SFXShannon/c172-home-sim/parts/mixture/stl/housing.stl

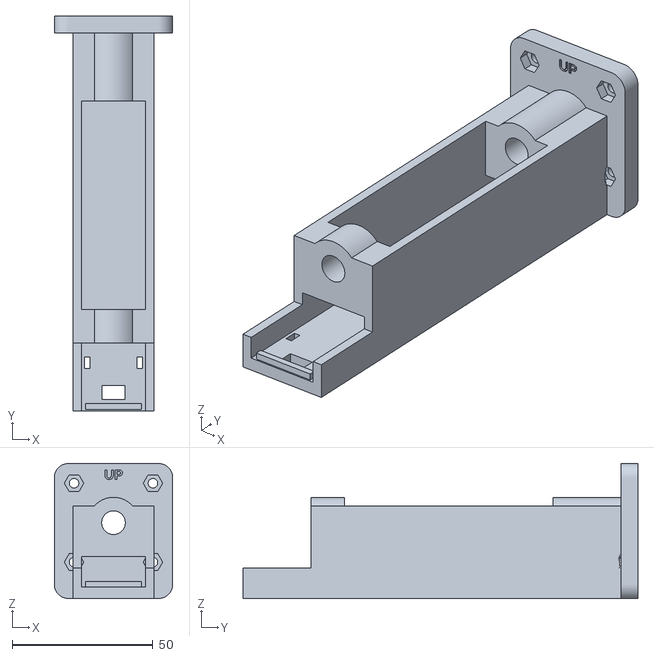
[picture p63: CAD file, 2026-10-08]
parts/mixture/stl/housing.stl
42.0 x 140.0 x 47.9
