SFXShannon/c172-home-sim/parts/panel-extras/stl/stem_clip.stl

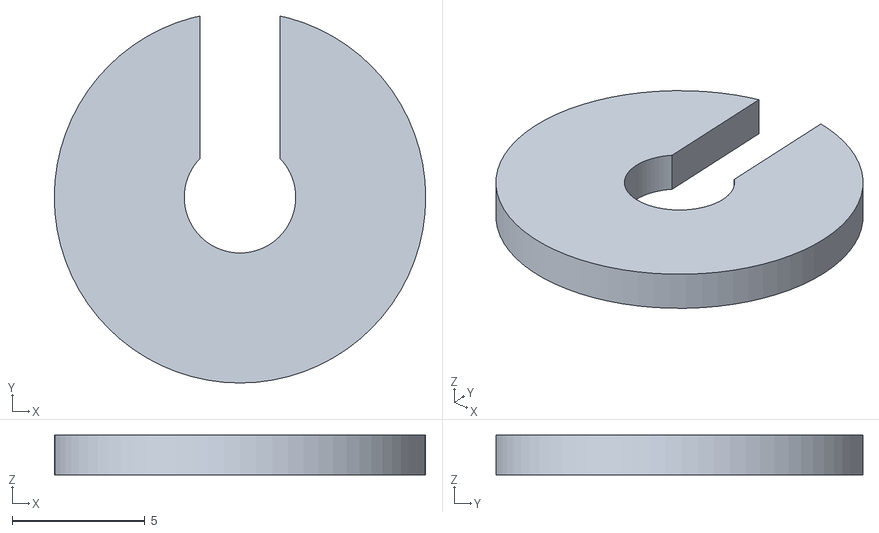
[picture p64: CAD file, 2026-10-08]
parts/panel-extras/stl/stem_clip.stl
14.0 x 13.8 x 1.50
