SFXShannon/c172-home-sim/parts/parking-brake/panel-template/parking_brake_cutout.dxf

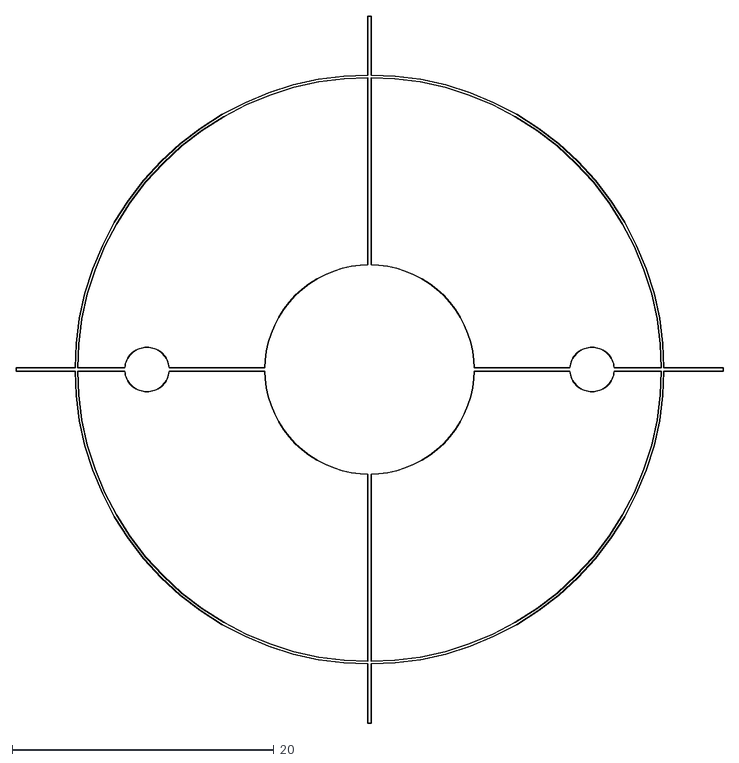
[picture p65: CAD file, 2026-10-08]
parts/parking-brake/panel-template/parking_brake_cutout.dxf
54.0 x 54.0
