SFXShannon/c172-home-sim/parts/parking-brake/stl/housing.stl

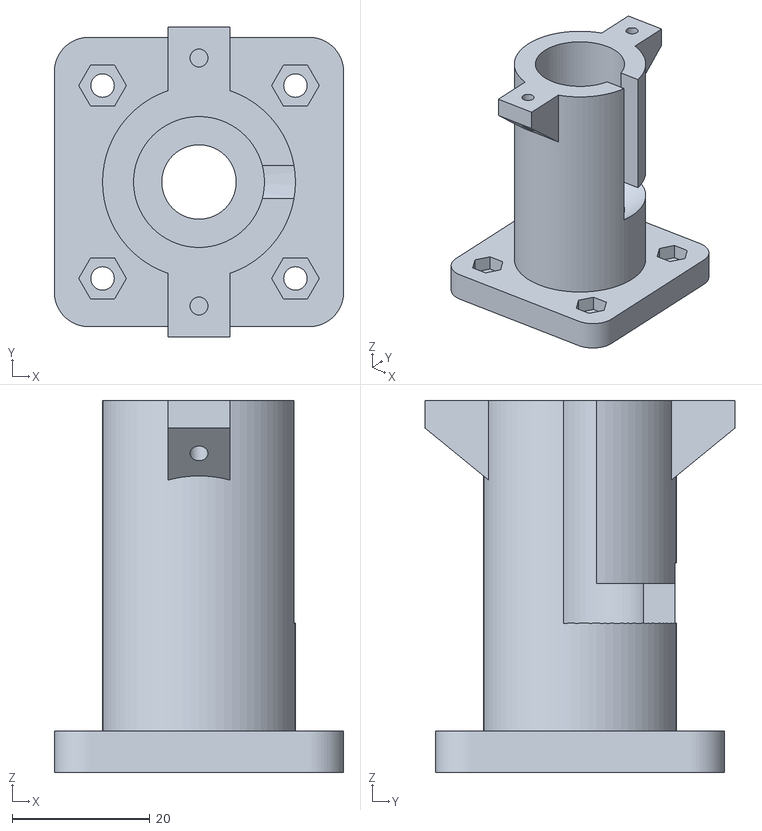
[picture p66: CAD file, 2026-10-08]
parts/parking-brake/stl/housing.stl
42.0 x 45.0 x 54.0
