SFXShannon/c172-home-sim/parts/prop/stl/knob.stl

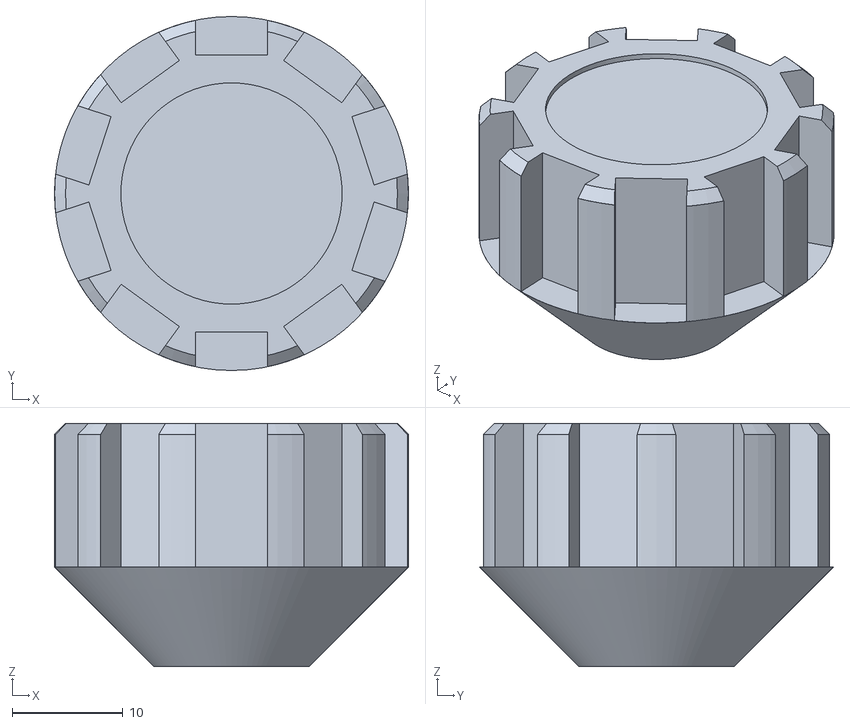
[picture p67: CAD file, 2026-10-08]
parts/prop/stl/knob.stl
32.0 x 32.0 x 22.0
