SFXShannon/c172-home-sim/parts/standby-gauges/panel-template/standby_gauges_cutout.dxf

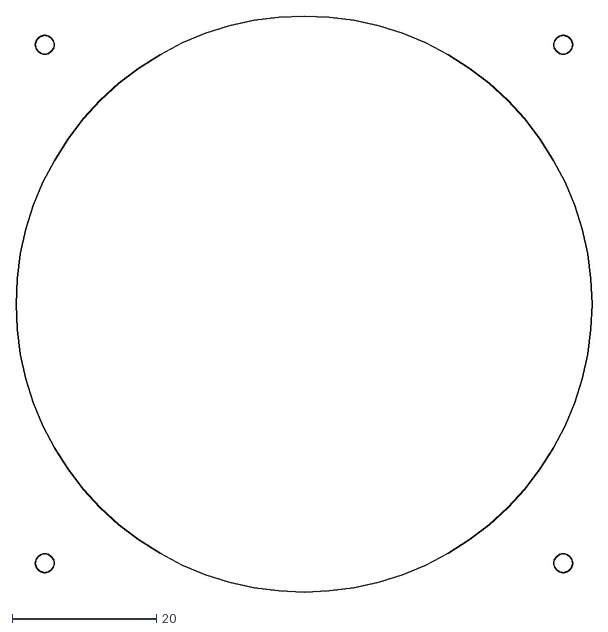
[picture p68: CAD file, 2026-10-08]
parts/standby-gauges/panel-template/standby_gauges_cutout.dxf
80.0 x 80.0
