SFXShannon/c172-home-sim/parts/standby-gauges/stl/face_disc.stl

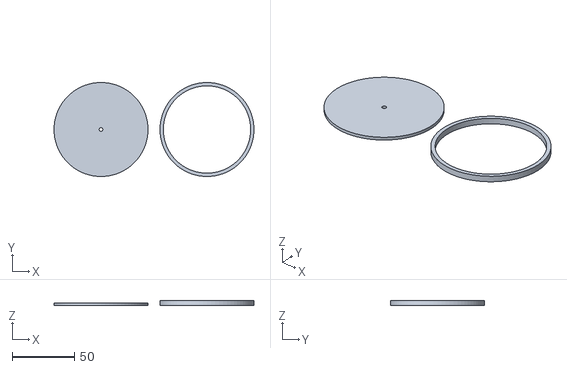
[picture p69: CAD file, 2026-10-08]
parts/standby-gauges/stl/face_disc.stl
160.4 x 75.4 x 4.00
