SFXShannon/c172-home-sim/parts/switch-panel/panel-template/lower_cutout.dxf

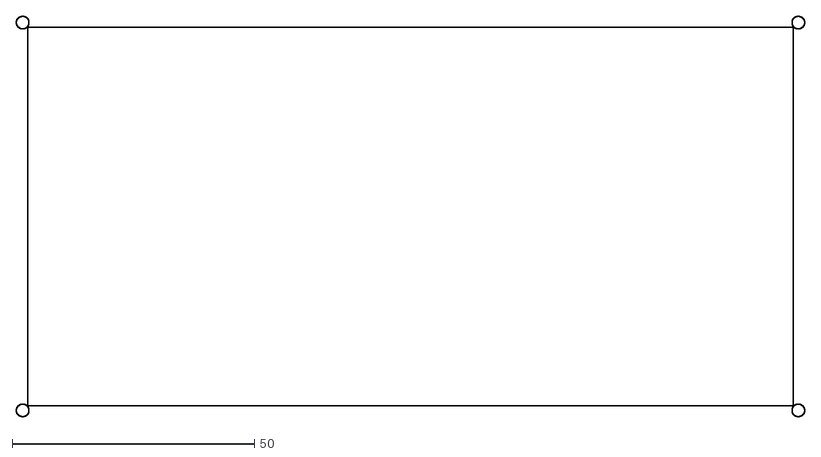
[picture p70: CAD file, 2026-10-08]
parts/switch-panel/panel-template/lower_cutout.dxf
162.6 x 82.6
