SFXShannon/c172-home-sim/parts/switch-panel/stl/dimmer_knob.stl

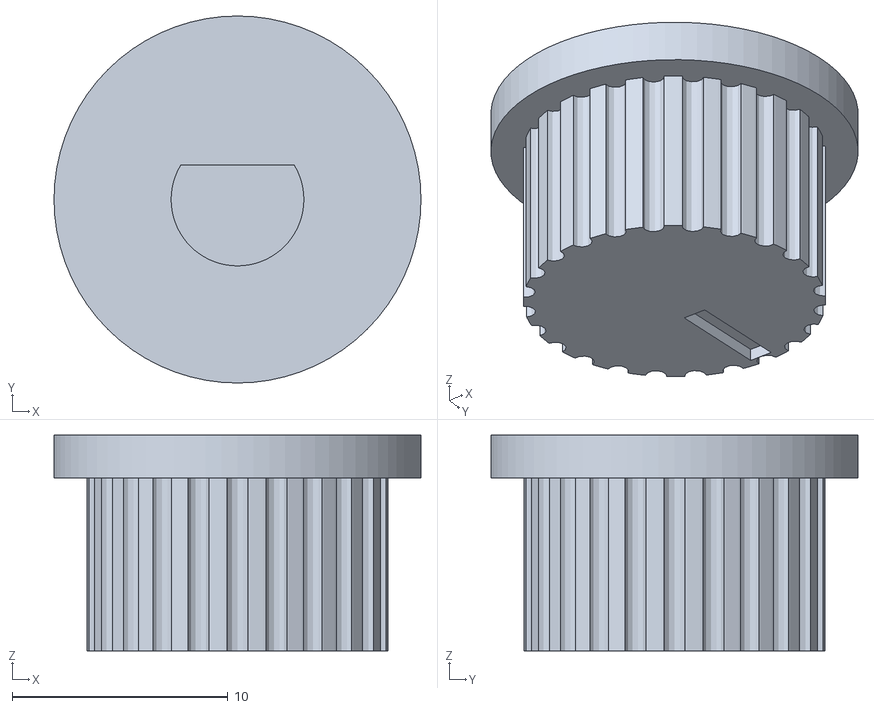
[picture p71: CAD file, 2026-10-08]
parts/switch-panel/stl/dimmer_knob.stl
17.0 x 17.0 x 10.0
