SFXShannon/c172-home-sim/parts/throttle/stl/escutcheon.stl

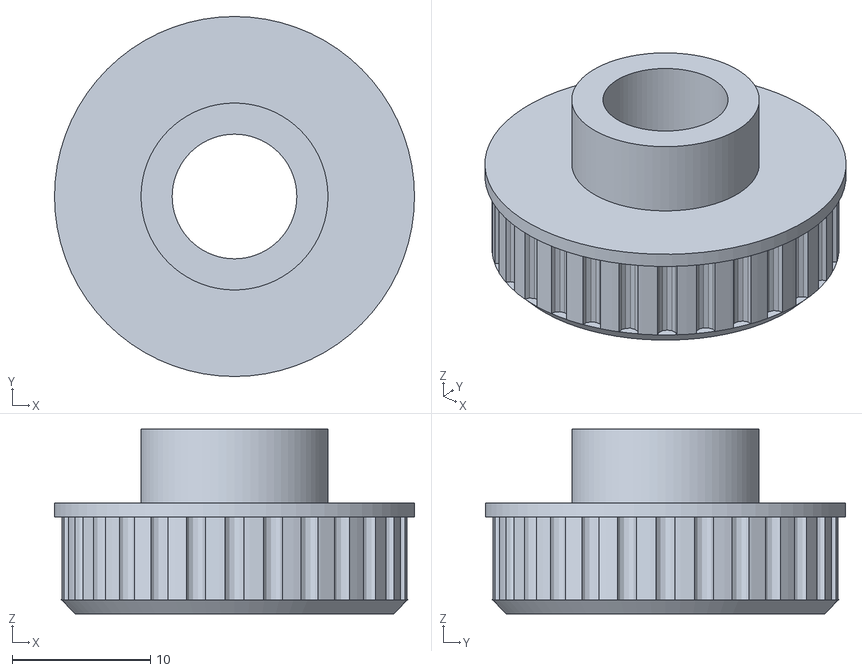
[picture p72: CAD file, 2026-10-08]
parts/throttle/stl/escutcheon.stl
26.0 x 26.0 x 13.3
