SFXShannon/c172-home-sim/parts/trim-wheel/panel-template/trim_wheel_cutout.dxf

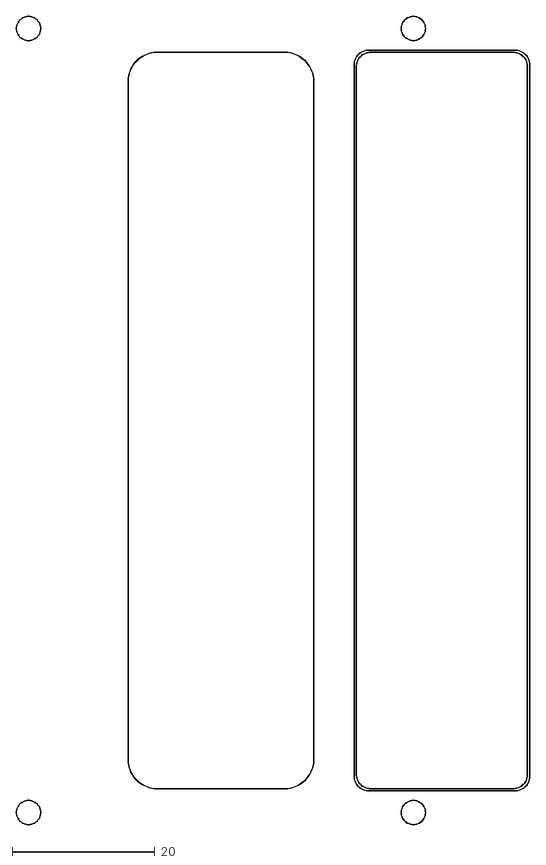
[picture p73: CAD file, 2026-10-08]
parts/trim-wheel/panel-template/trim_wheel_cutout.dxf
72.0 x 113.4
