SFXShannon/c172-home-sim/parts/trim-wheel/stl/panel_test_plate.stl

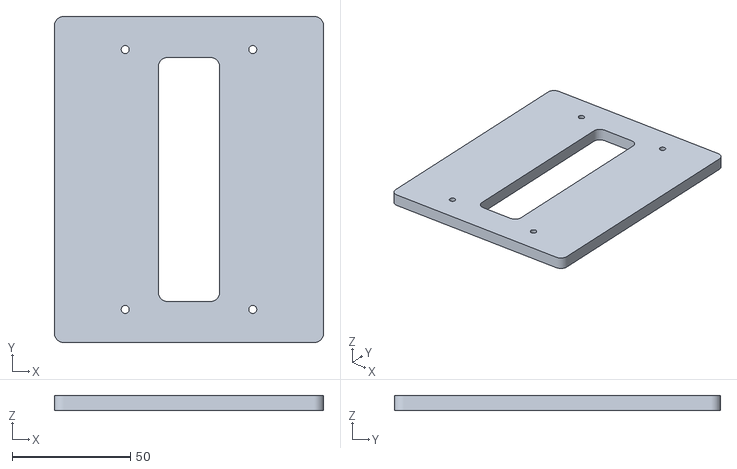
[picture p74: CAD file, 2026-10-08]
parts/trim-wheel/stl/panel_test_plate.stl
114.0 x 138.0 x 6.35
