SFXShannon/c172-home-sim/panel/dashboard/cnc/lower_1_back.dxf

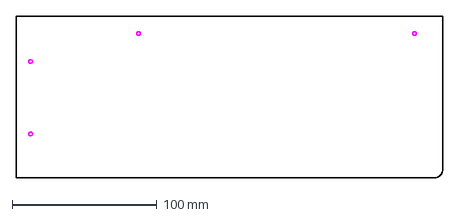
[picture p75: CAD file, 2026-10-08]
panel/dashboard/cnc/lower_1_back.dxf
295.0 x 112.0 mm
