SFXShannon/c172-home-sim/panel/dashboard/stl/glareshield_3.stl

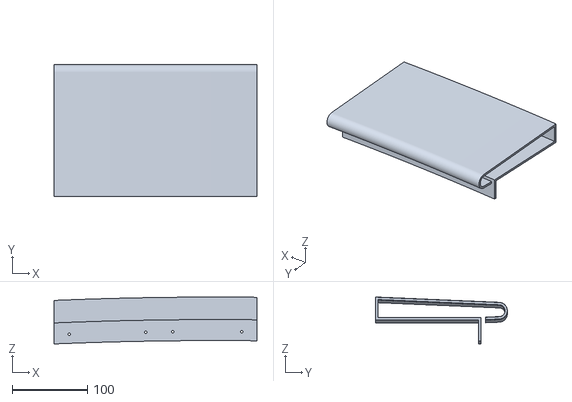
[picture p76: CAD file, 2026-10-08]
panel/dashboard/stl/glareshield_3.stl
270.5 x 175.3 x 62.5
