SFXShannon/c172-home-sim/panel/stl/lower_tile_1.stl

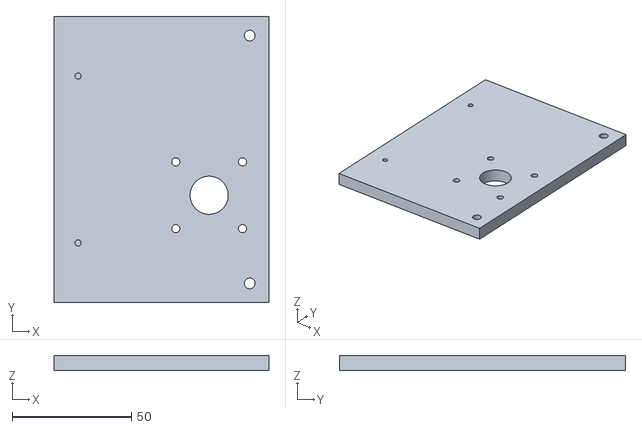
[picture p77: CAD file, 2026-10-08]
panel/stl/lower_tile_1.stl
90.0 x 120.0 x 6.35
