SFXShannon/c172-home-sim/panel/templates/lower_panel.dxf

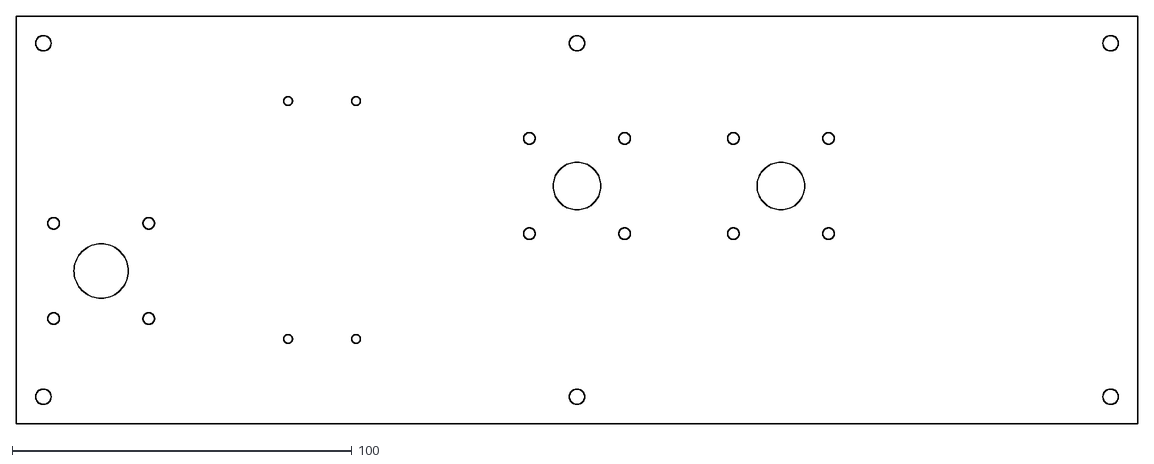
[picture p78: CAD file, 2026-10-08]
panel/templates/lower_panel.dxf
330.0 x 120.0
