SFXShannon/c172-home-sim/parts/flap-lever/stl/housing.stl

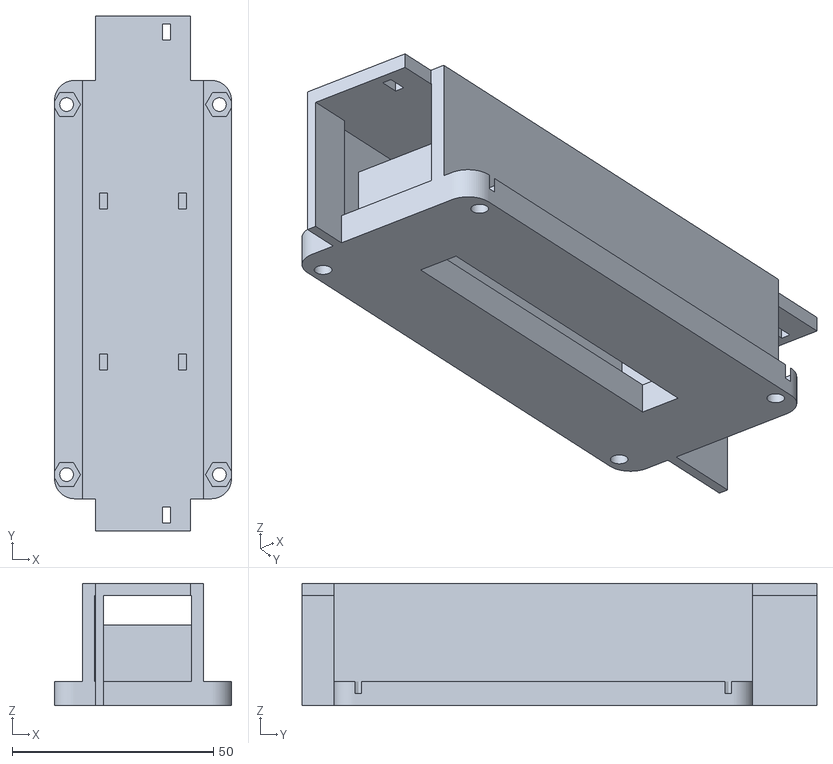
[picture p79: CAD file, 2026-10-08]
parts/flap-lever/stl/housing.stl
44.0 x 128.0 x 30.4
