SFXShannon/c172-home-sim/parts/fuel-selector/stl/placard.stl

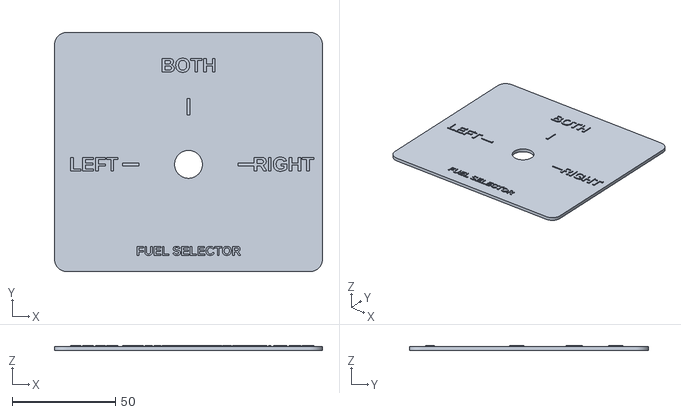
[picture p80: CAD file, 2026-10-08]
parts/fuel-selector/stl/placard.stl
130.0 x 116.0 x 2.59
