SFXShannon/c172-home-sim/parts/g1000-gdu/stl/front_right.stl

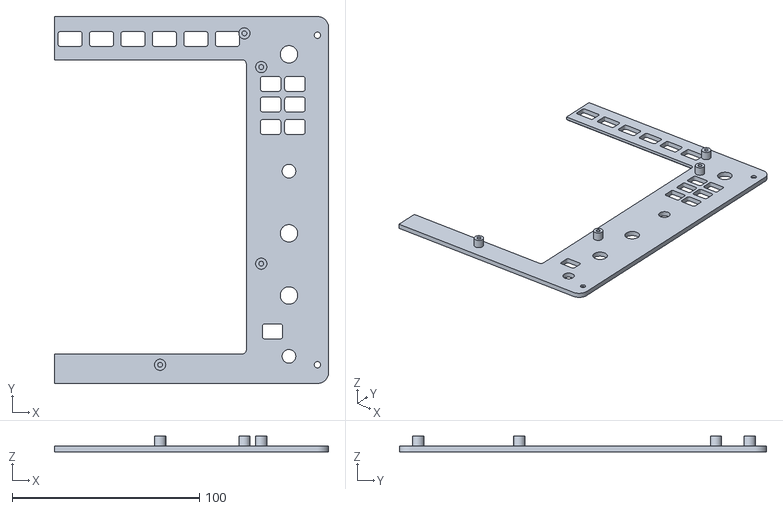
[picture p81: CAD file, 2026-10-08]
parts/g1000-gdu/stl/front_right.stl
146.5 x 196.0 x 8.40
