SFXShannon/c172-home-sim/parts/g1000-gma/stl/knob.stl

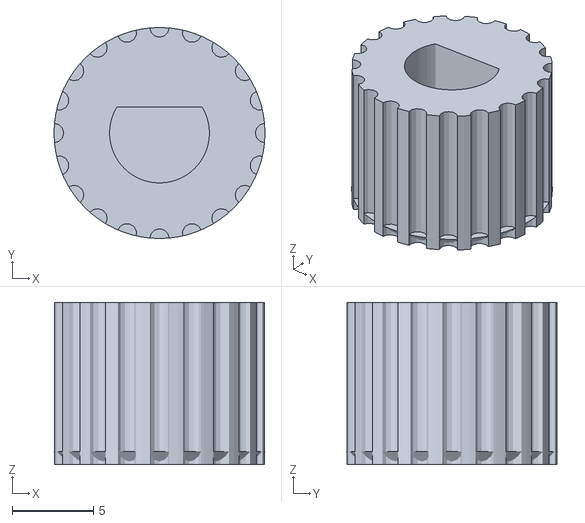
[picture p82: CAD file, 2026-10-08]
parts/g1000-gma/stl/knob.stl
13.0 x 13.0 x 10.0
