SFXShannon/c172-home-sim/parts/mixture/stl/carriage.stl

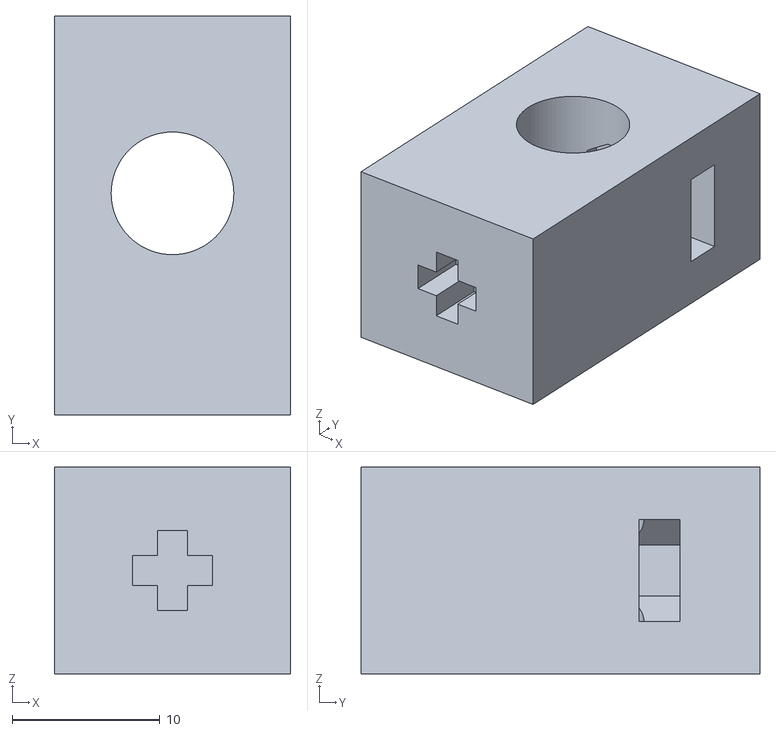
[picture p83: CAD file, 2026-10-08]
parts/mixture/stl/carriage.stl
16.0 x 27.0 x 14.0
