SFXShannon/c172-home-sim/parts/panel-extras/stl/yoke_boot.stl

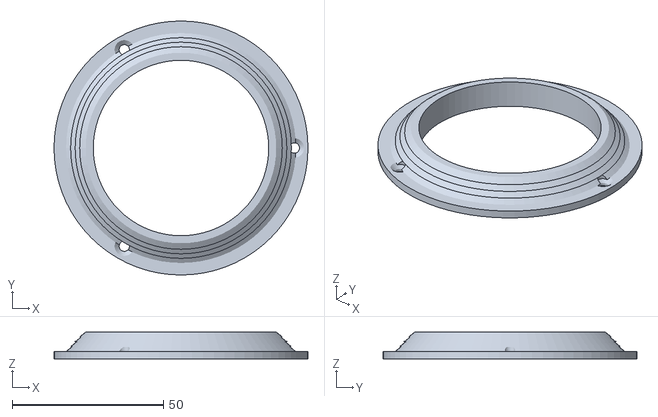
[picture p84: CAD file, 2026-10-08]
parts/panel-extras/stl/yoke_boot.stl
84.0 x 84.0 x 8.91
