SFXShannon/c172-home-sim/parts/parking-brake/stl/shaft.stl

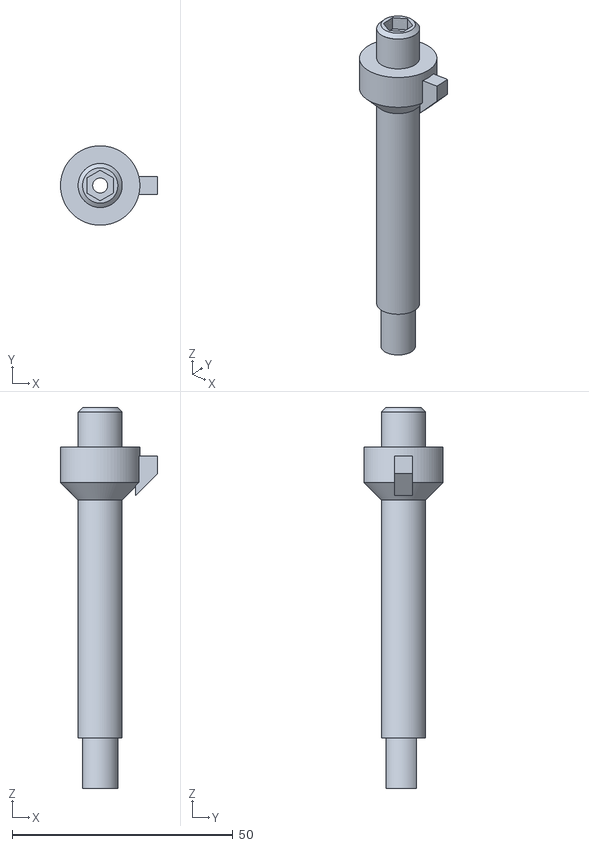
[picture p85: CAD file, 2026-10-08]
parts/parking-brake/stl/shaft.stl
22.0 x 18.0 x 86.3
