SFXShannon/c172-home-sim/parts/standby-gauges/stl/case.stl

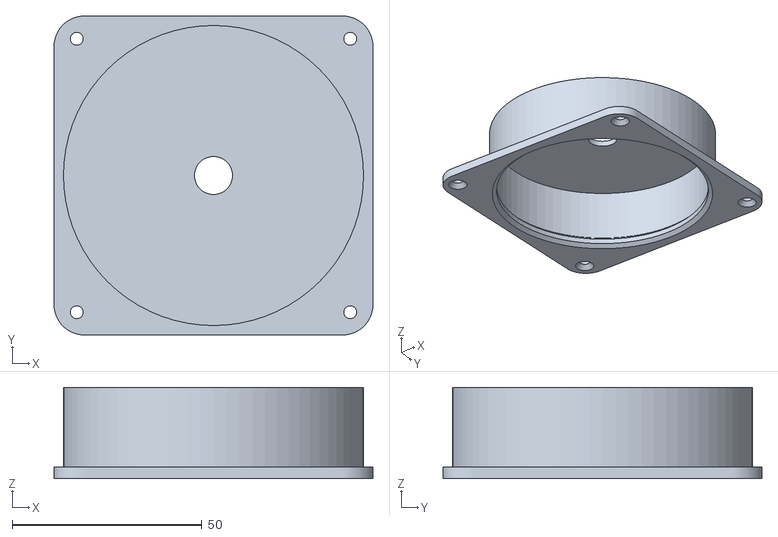
[picture p86: CAD file, 2026-10-08]
parts/standby-gauges/stl/case.stl
84.0 x 84.0 x 24.0
