SFXShannon/c172-home-sim/parts/switch-panel/panel-template/upper_cutout.dxf

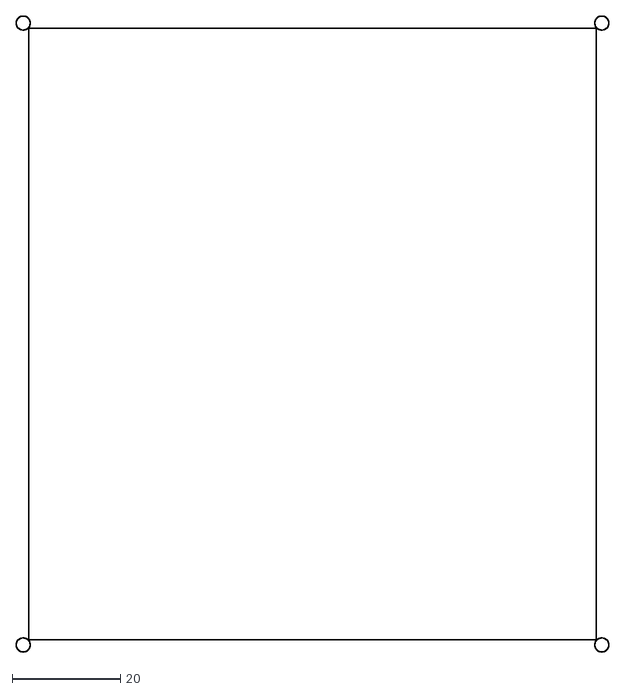
[picture p87: CAD file, 2026-10-08]
parts/switch-panel/panel-template/upper_cutout.dxf
109.6 x 117.6
