SFXShannon/c172-home-sim/parts/switch-panel/stl/lower_plate.stl

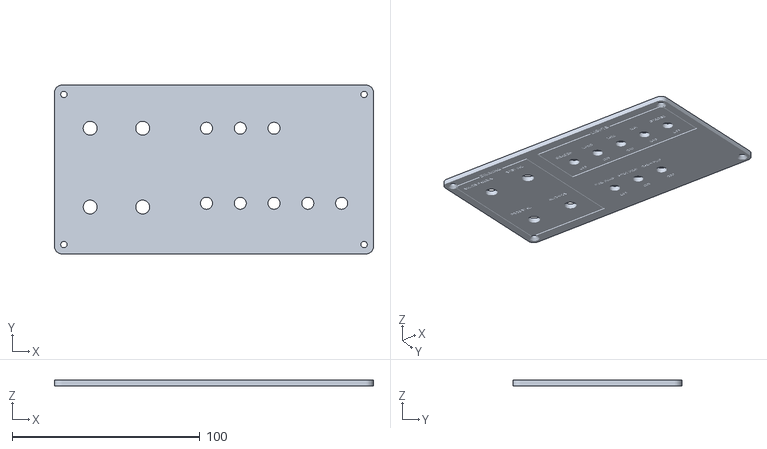
[picture p88: CAD file, 2026-10-08]
parts/switch-panel/stl/lower_plate.stl
170.0 x 90.0 x 3.00
