SFXShannon/c172-home-sim/parts/trim-wheel/stl/wheel.stl

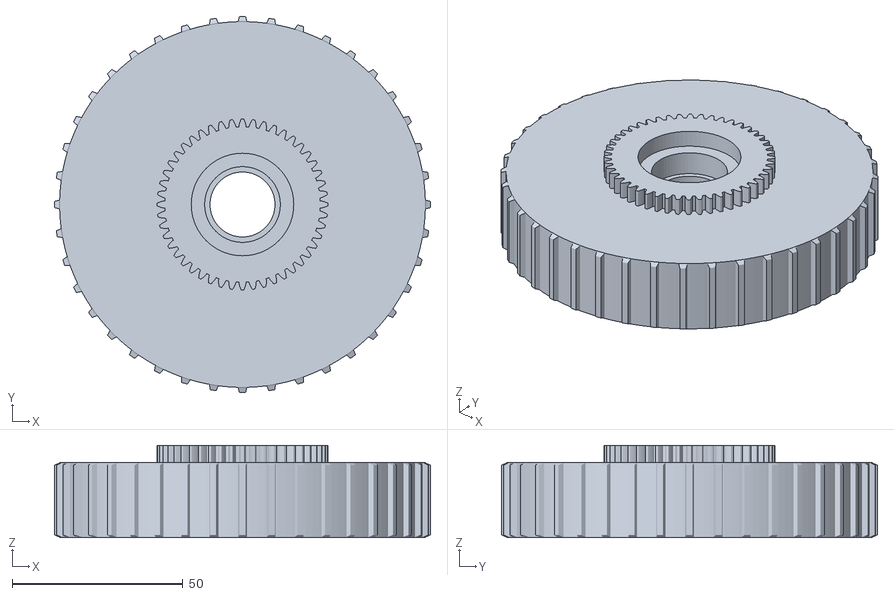
[picture p89: CAD file, 2026-10-08]
parts/trim-wheel/stl/wheel.stl
110.0 x 110.0 x 27.0
