SFXShannon/c172-home-sim/panel/dashboard/cnc/lower_2_back.dxf

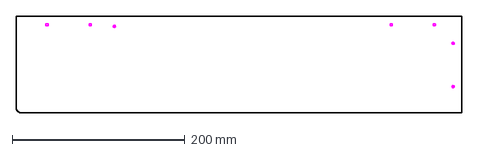
[picture p90: CAD file, 2026-10-08]
panel/dashboard/cnc/lower_2_back.dxf
515.0 x 112.0 mm
