SFXShannon/c172-home-sim/panel/dashboard/stl/tile_U3.stl

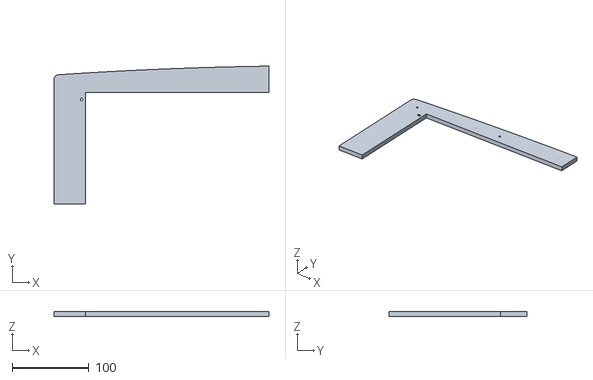
[picture p91: CAD file, 2026-10-08]
panel/dashboard/stl/tile_U3.stl
280.0 x 179.5 x 6.35
