SFXShannon/c172-home-sim/panel/stl/splice.stl

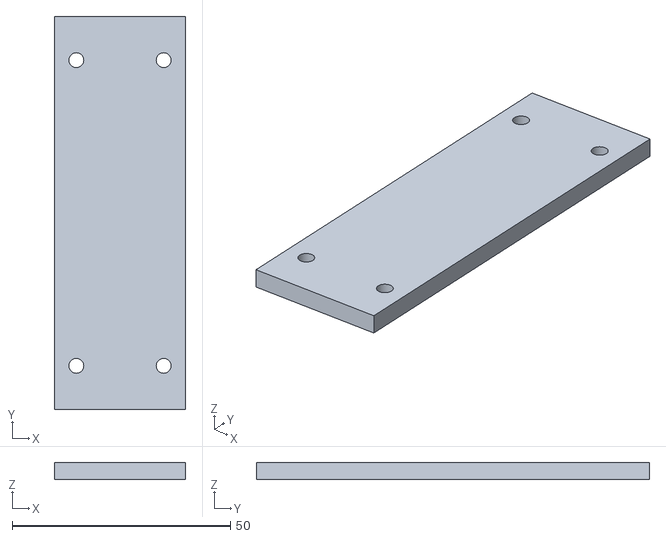
[picture p92: CAD file, 2026-10-08]
panel/stl/splice.stl
30.0 x 90.0 x 4.00
