SFXShannon/c172-home-sim/panel/templates/floor_panel.dxf

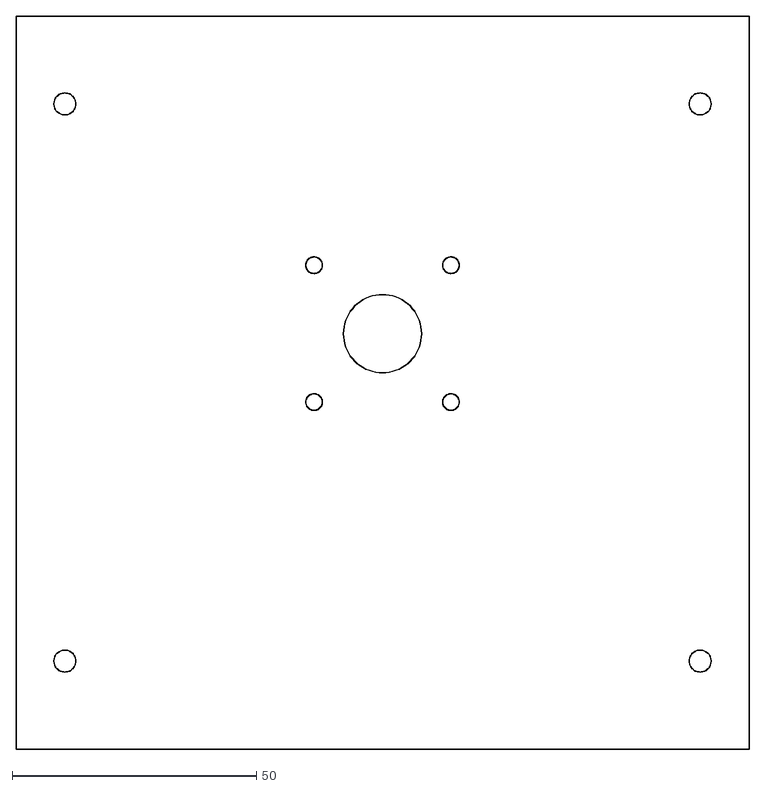
[picture p93: CAD file, 2026-10-08]
panel/templates/floor_panel.dxf
150.0 x 150.0
