SFXShannon/c172-home-sim/parts/flap-lever/stl/handle.stl

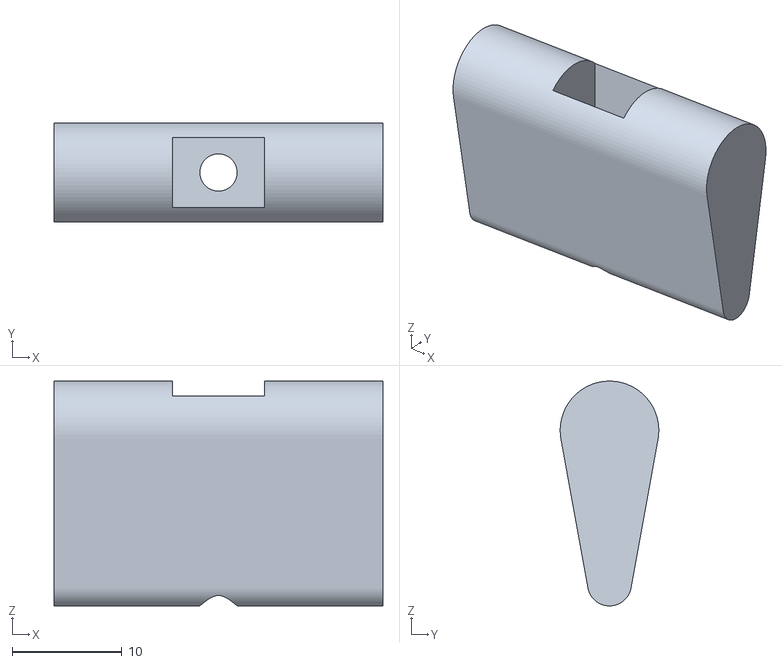
[picture p94: CAD file, 2026-10-08]
parts/flap-lever/stl/handle.stl
30.0 x 9.00 x 20.5
