SFXShannon/c172-home-sim/parts/fuel-selector/stl/switch_gear.stl

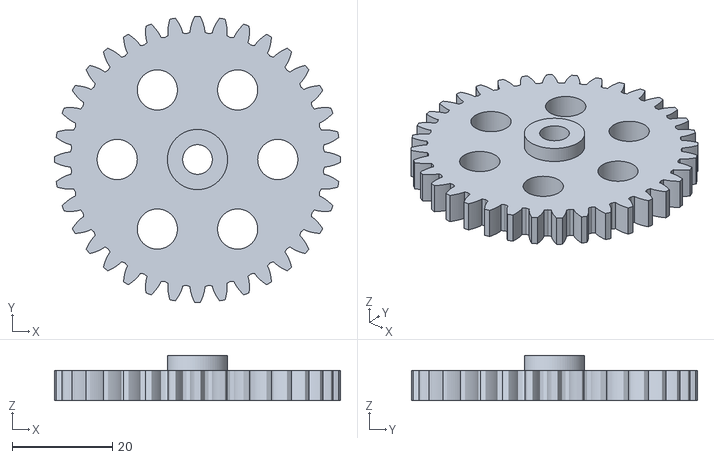
[picture p95: CAD file, 2026-10-08]
parts/fuel-selector/stl/switch_gear.stl
57.0 x 57.0 x 9.00
