SFXShannon/c172-home-sim/parts/g1000-gdu/stl/switch_plate.stl

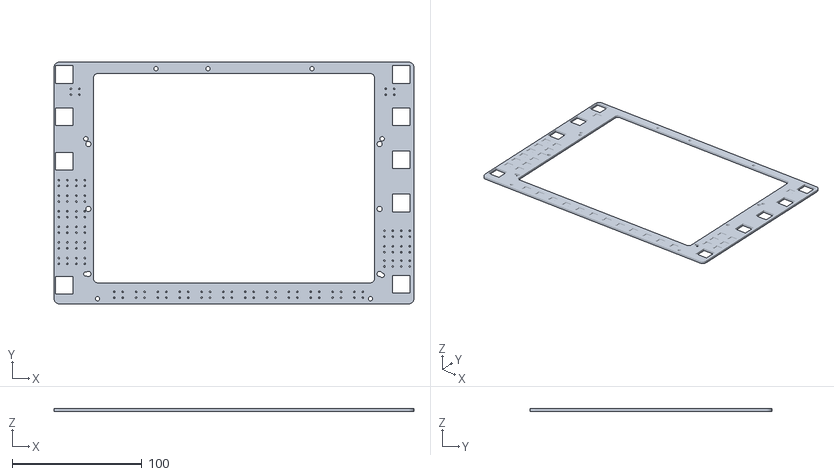
[picture p96: CAD file, 2026-10-08]
parts/g1000-gdu/stl/switch_plate.stl
277.0 x 186.0 x 2.50
