SFXShannon/c172-home-sim/parts/g1000-gma/stl/caps_sheet.stl

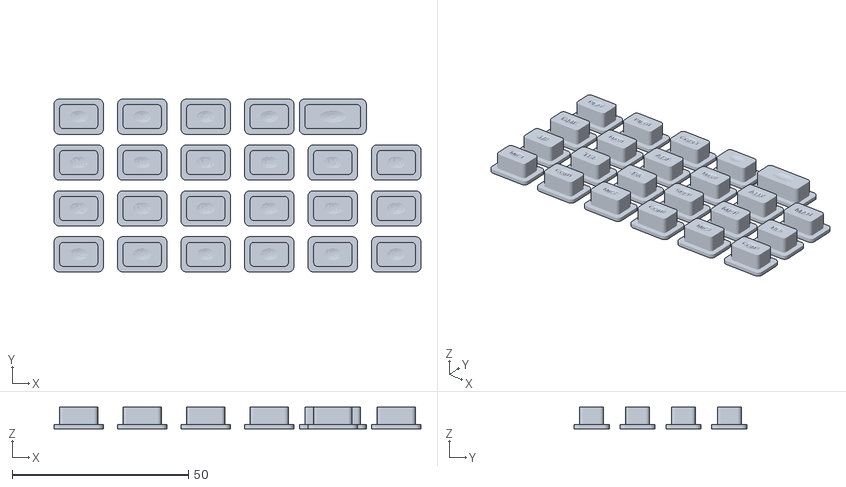
[picture p97: CAD file, 2026-10-08]
parts/g1000-gma/stl/caps_sheet.stl
104.0 x 49.0 x 6.20
