SFXShannon/c172-home-sim/parts/mixture/stl/escutcheon.stl

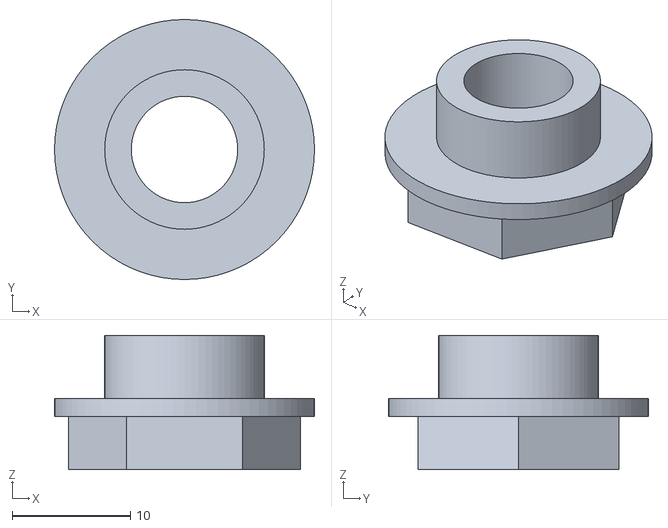
[picture p98: CAD file, 2026-10-08]
parts/mixture/stl/escutcheon.stl
22.0 x 22.0 x 11.3
