SFXShannon/c172-home-sim/parts/panel-extras/stl/knob_stem.stl

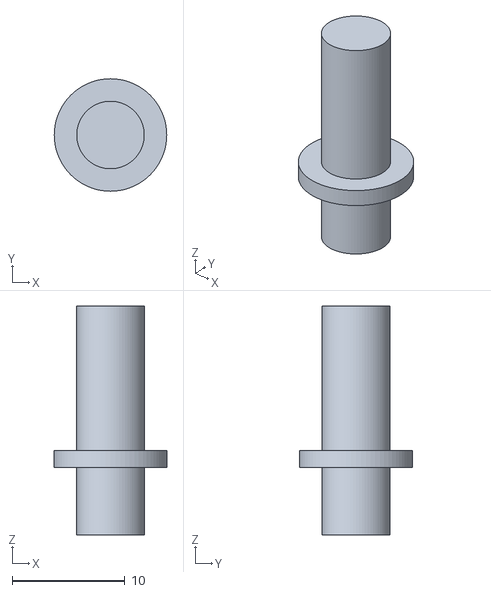
[picture p99: CAD file, 2026-10-08]
parts/panel-extras/stl/knob_stem.stl
10.0 x 10.0 x 20.4
