SFXShannon/c172-home-sim/parts/parking-brake/stl/handle.stl

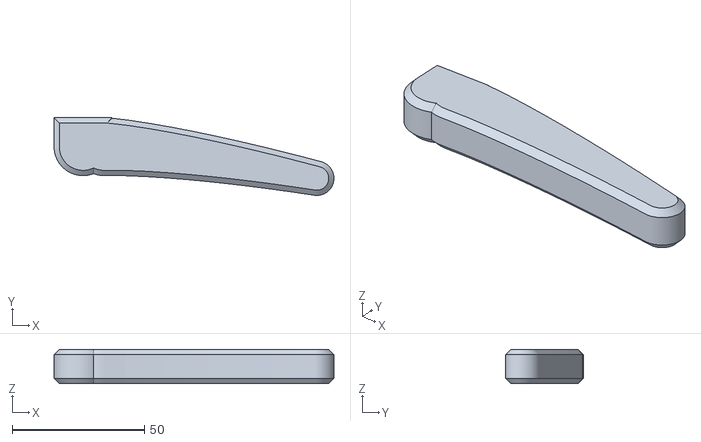
[picture p100: CAD file, 2026-10-08]
parts/parking-brake/stl/handle.stl
106.0 x 29.5 x 13.0
