SFXShannon/c172-home-sim/parts/switch-panel/stl/upper_plate.stl

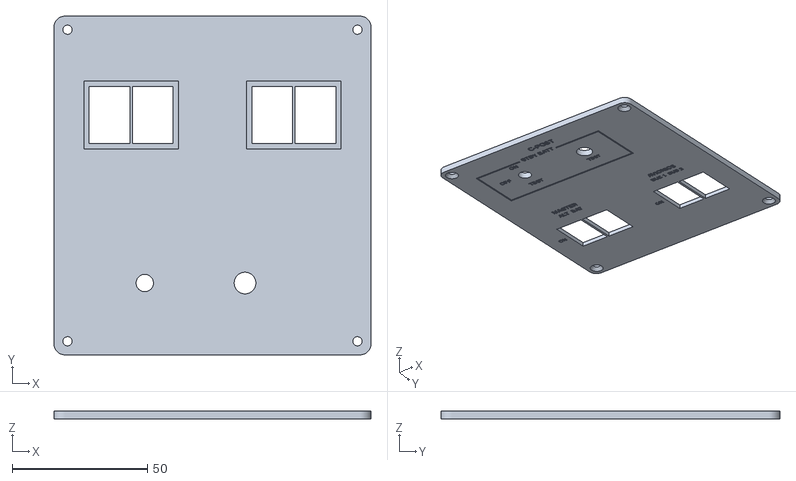
[picture p101: CAD file, 2026-10-08]
parts/switch-panel/stl/upper_plate.stl
117.0 x 125.0 x 3.00
