SFXShannon/c172-home-sim/parts/throttle/stl/knob.stl

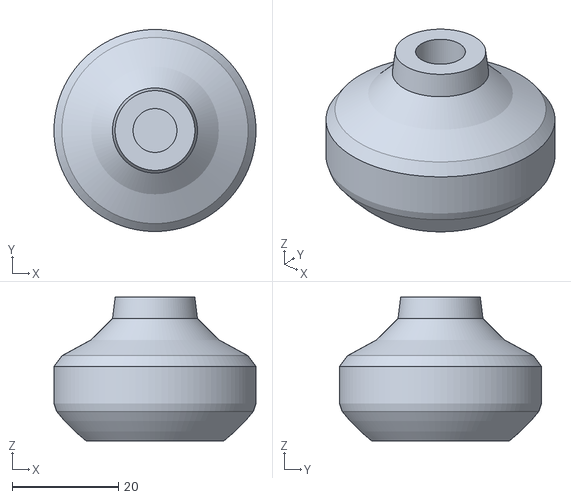
[picture p102: CAD file, 2026-10-08]
parts/throttle/stl/knob.stl
38.0 x 38.0 x 27.0
