SFXShannon/c172-home-sim/parts/trim-wheel/stl/encoder_gear.stl

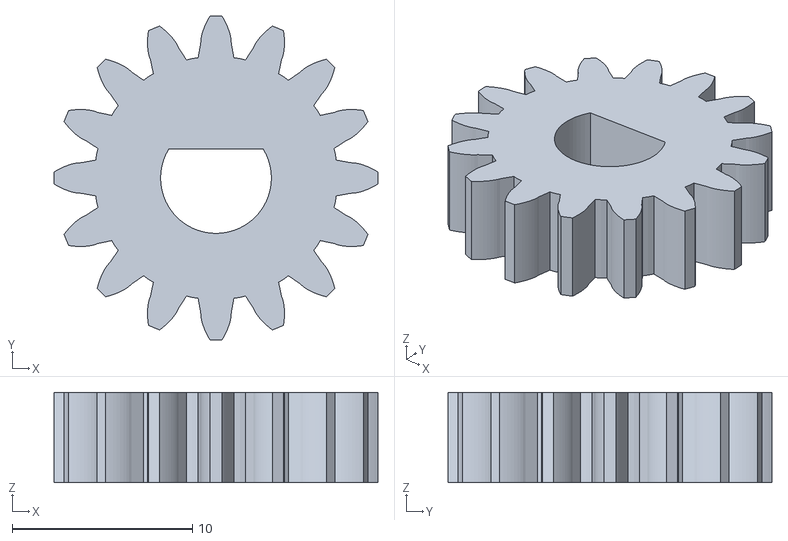
[picture p103: CAD file, 2026-10-08]
parts/trim-wheel/stl/encoder_gear.stl
18.0 x 18.0 x 5.00
