SFXShannon/c172-home-sim/panel/dashboard/cnc/upper_1_back.dxf

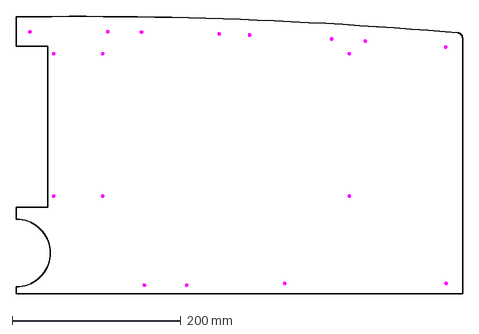
[picture p104: CAD file, 2026-10-08]
panel/dashboard/cnc/upper_1_back.dxf
528.0 x 328.0 mm
