SFXShannon/c172-home-sim/panel/dashboard/stl/splice.stl

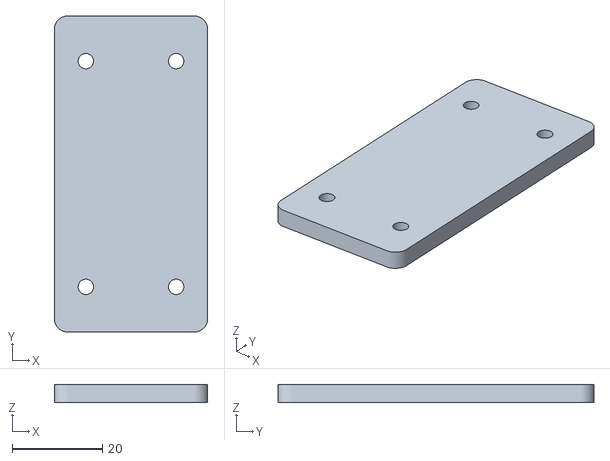
[picture p105: CAD file, 2026-10-08]
panel/dashboard/stl/splice.stl
34.0 x 70.0 x 4.00
