SFXShannon/c172-home-sim/panel/stl/lower_tile_2.stl

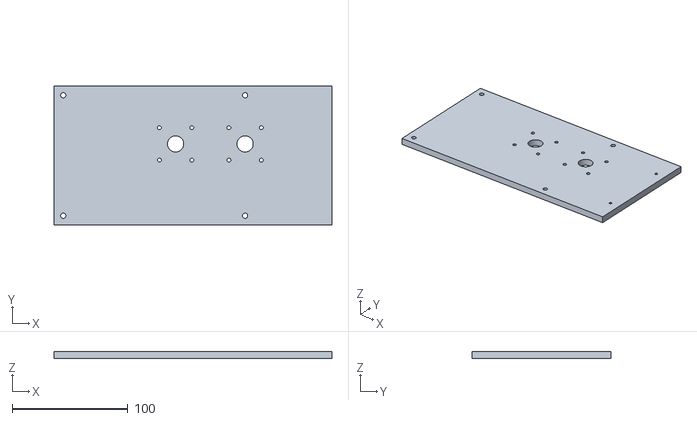
[picture p106: CAD file, 2026-10-08]
panel/stl/lower_tile_2.stl
240.0 x 120.0 x 6.35
