SFXShannon/c172-home-sim/parts/fuel-selector/stl/shaft.stl

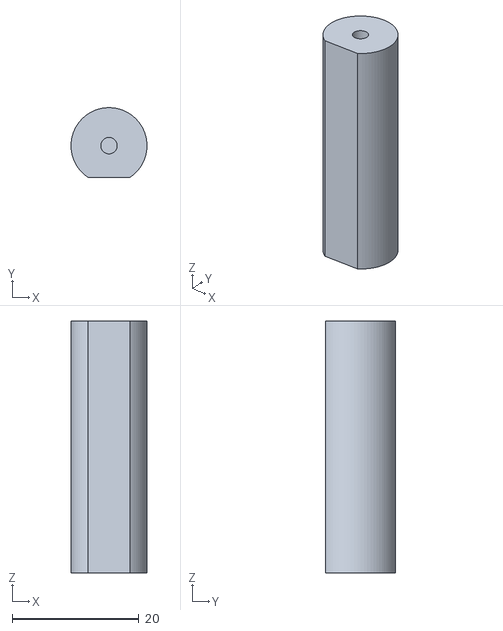
[picture p107: CAD file, 2026-10-08]
parts/fuel-selector/stl/shaft.stl
12.0 x 11.0 x 39.7
