SFXShannon/c172-home-sim/parts/g1000-gdu/stl/front.stl

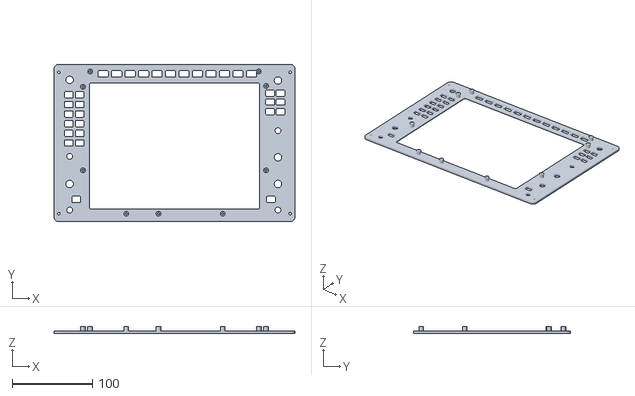
[picture p108: CAD file, 2026-10-08]
parts/g1000-gdu/stl/front.stl
300.0 x 196.0 x 8.40
