SFXShannon/c172-home-sim/parts/g1000-gma/stl/front.stl

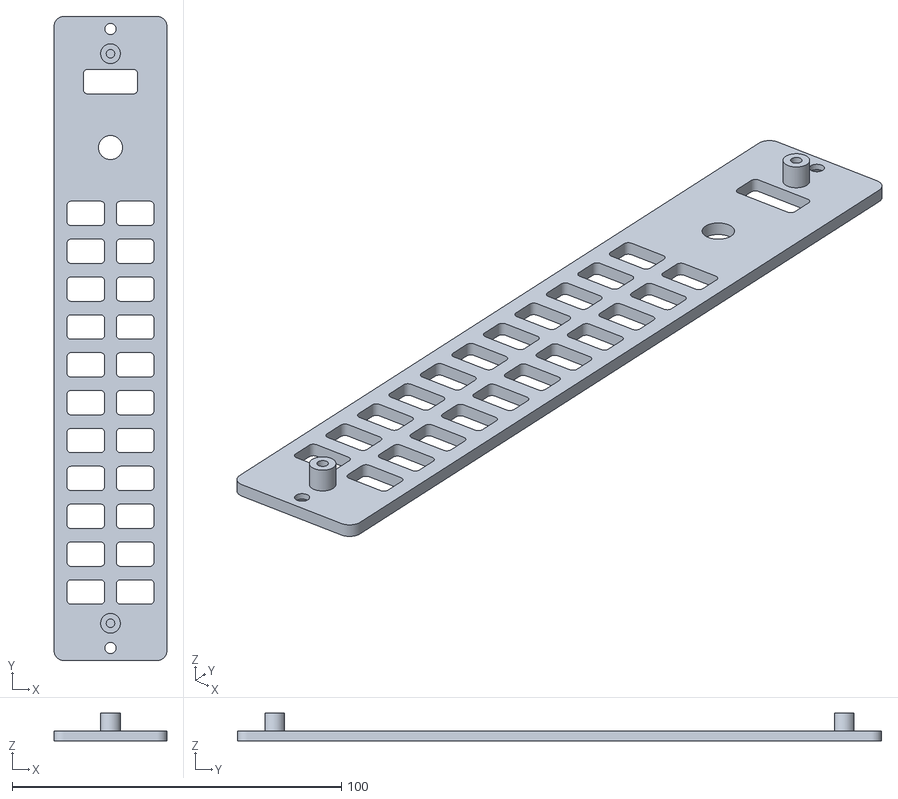
[picture p109: CAD file, 2026-10-08]
parts/g1000-gma/stl/front.stl
34.3 x 195.6 x 8.40
