SFXShannon/c172-home-sim/parts/mixture/stl/knob.stl

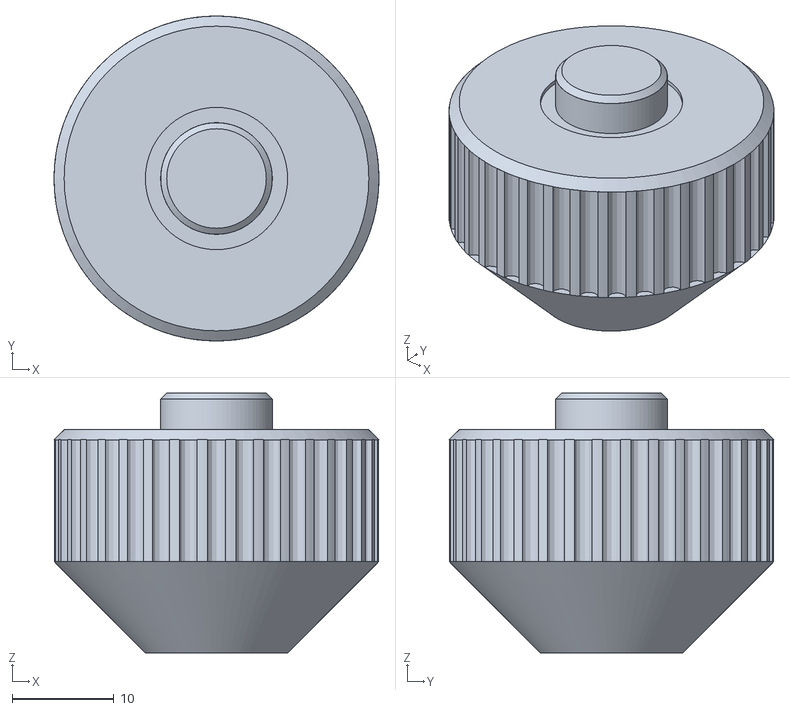
[picture p110: CAD file, 2026-10-08]
parts/mixture/stl/knob.stl
32.0 x 32.0 x 25.6
