SFXShannon/c172-home-sim/parts/panel-extras/stl/knob_alt_static.stl

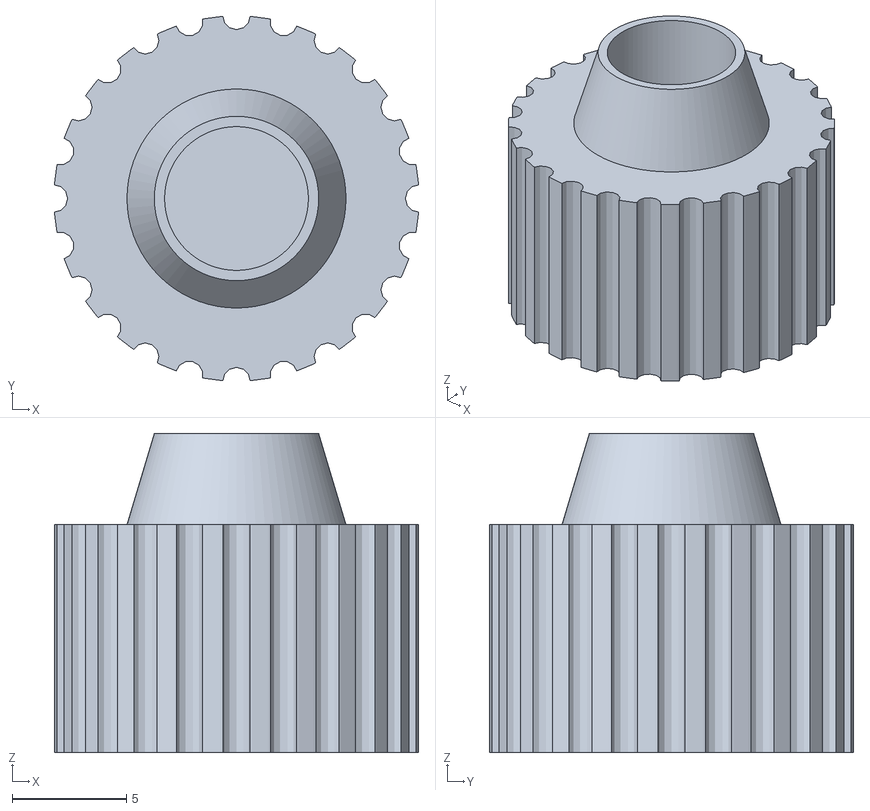
[picture p111: CAD file, 2026-10-08]
parts/panel-extras/stl/knob_alt_static.stl
15.9 x 15.9 x 14.0
