SFXShannon/c172-home-sim/parts/parking-brake/stl/escutcheon.stl

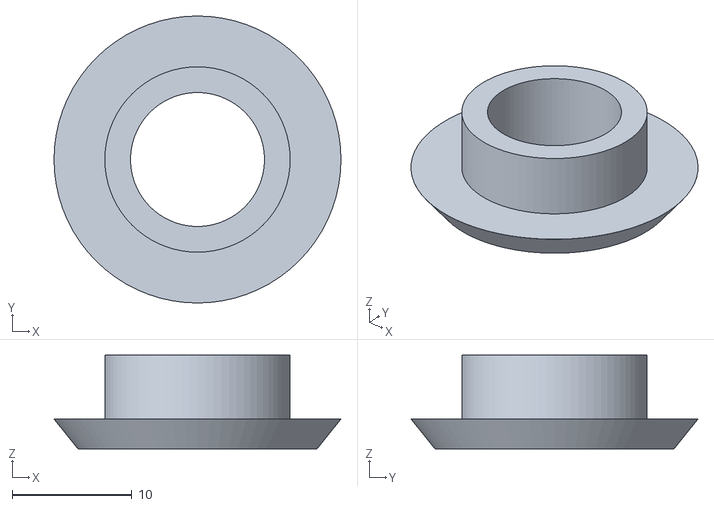
[picture p112: CAD file, 2026-10-08]
parts/parking-brake/stl/escutcheon.stl
24.0 x 24.0 x 7.84
