SFXShannon/c172-home-sim/parts/trim-wheel/stl/housing.stl

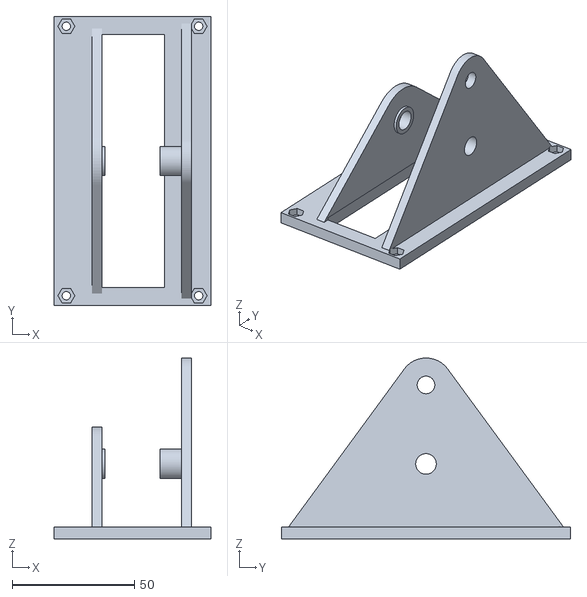
[picture p113: CAD file, 2026-10-08]
parts/trim-wheel/stl/housing.stl
64.0 x 118.0 x 73.9
