SFXShannon/c172-home-sim/panel/dashboard/cnc/upper_2_back.dxf

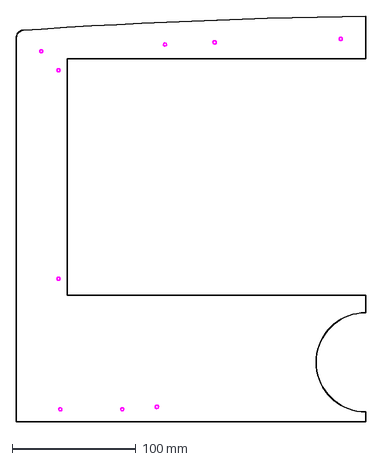
[picture p114: CAD file, 2026-10-08]
panel/dashboard/cnc/upper_2_back.dxf
282.0 x 327.5 mm
