SFXShannon/c172-home-sim/panel/dashboard/stl/glareshield_1.stl

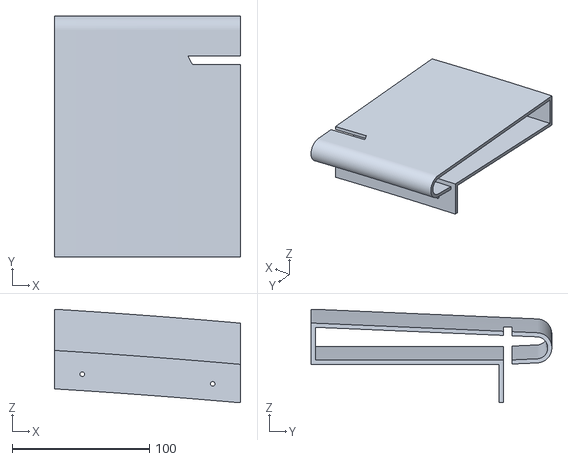
[picture p115: CAD file, 2026-10-08]
panel/dashboard/stl/glareshield_1.stl
135.5 x 175.3 x 68.1
