SFXShannon/c172-home-sim/panel/stl/floor.stl

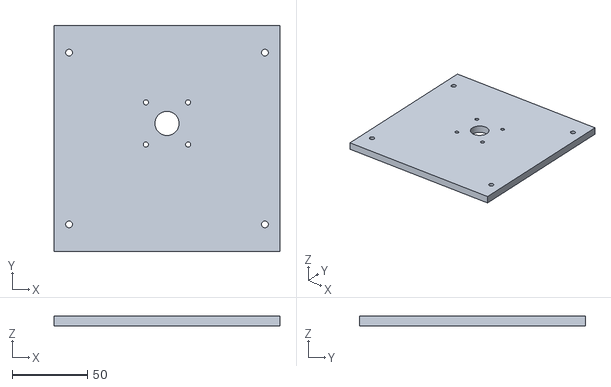
[picture p116: CAD file, 2026-10-08]
panel/stl/floor.stl
150.0 x 150.0 x 6.35
