SFXShannon/c172-home-sim/parts/fuel-selector/stl/housing.stl

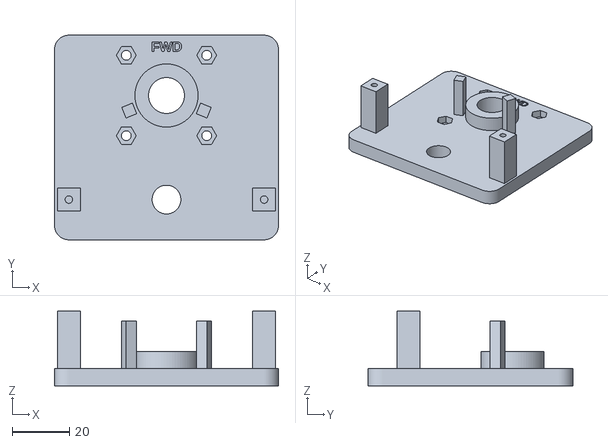
[picture p117: CAD file, 2026-10-08]
parts/fuel-selector/stl/housing.stl
78.0 x 71.2 x 26.0
