SFXShannon/c172-home-sim/parts/g1000-gdu/stl/front_left.stl

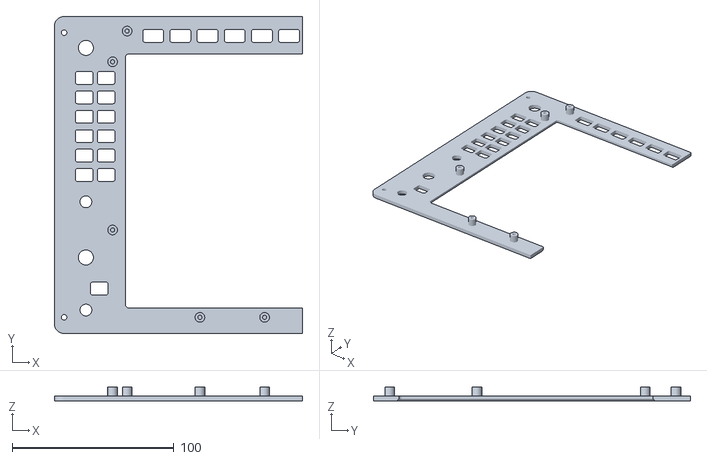
[picture p118: CAD file, 2026-10-08]
parts/g1000-gdu/stl/front_left.stl
153.5 x 196.0 x 8.40
