SFXShannon/c172-home-sim/parts/mixture/stl/panel_test_plate.stl

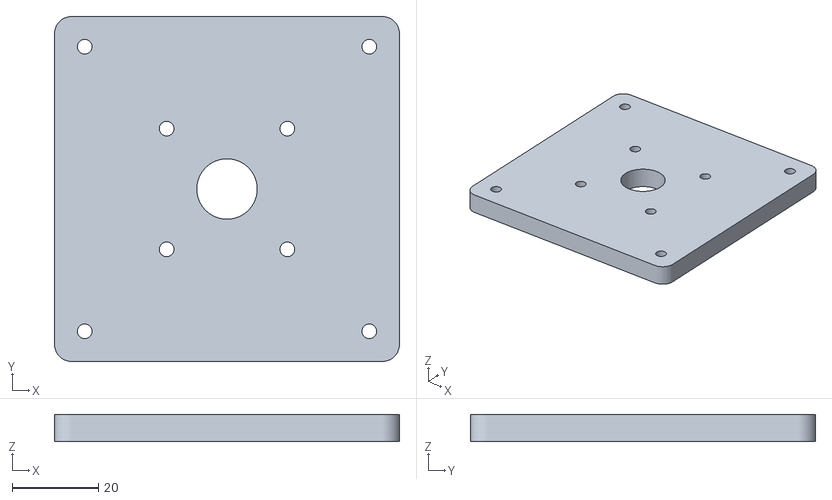
[picture p119: CAD file, 2026-10-08]
parts/mixture/stl/panel_test_plate.stl
80.0 x 80.0 x 6.35
