SFXShannon/c172-home-sim/parts/panel-extras/stl/cb_strip.stl

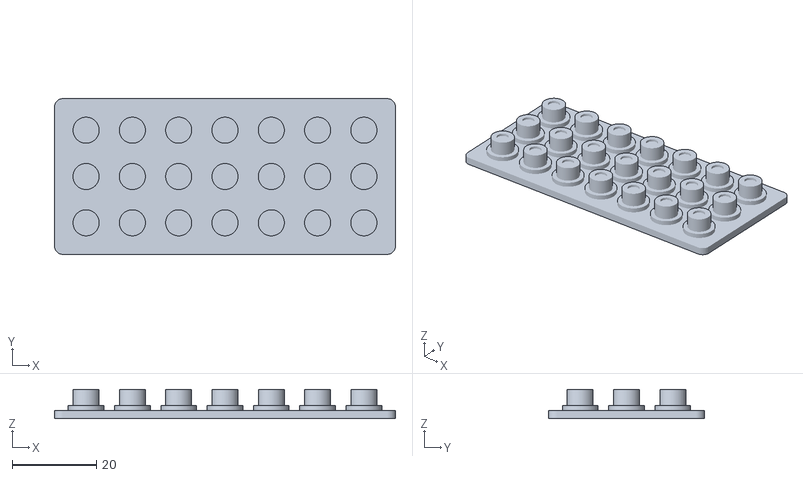
[picture p120: CAD file, 2026-10-08]
parts/panel-extras/stl/cb_strip.stl
81.0 x 37.0 x 6.99
