SFXShannon/c172-home-sim/parts/parking-brake/stl/rear_cap.stl

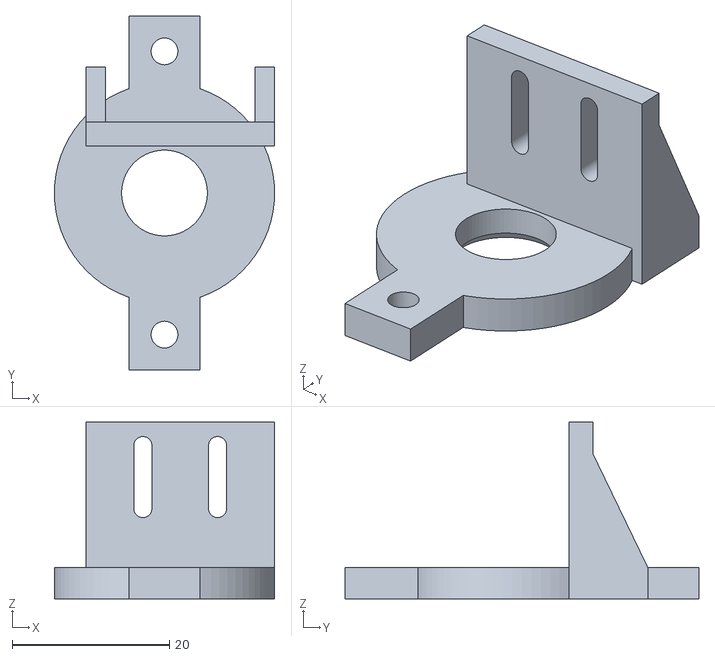
[picture p121: CAD file, 2026-10-08]
parts/parking-brake/stl/rear_cap.stl
28.0 x 45.0 x 22.5
