SFXShannon/c172-home-sim/parts/trim-wheel/stl/placard.stl

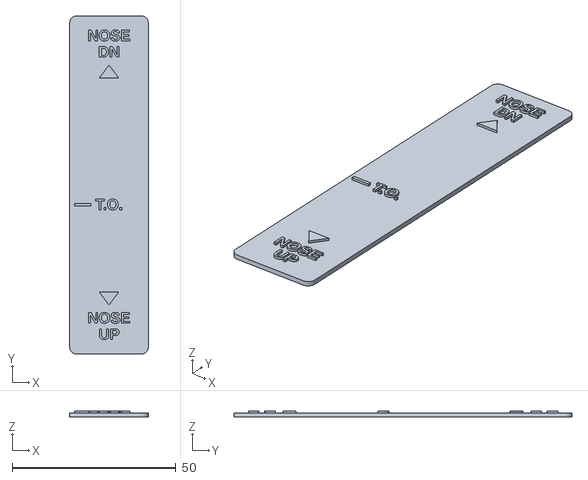
[picture p122: CAD file, 2026-10-08]
parts/trim-wheel/stl/placard.stl
24.0 x 103.3 x 1.80
