SFXShannon/c172-home-sim/panel/dashboard/cnc/splice_small.dxf

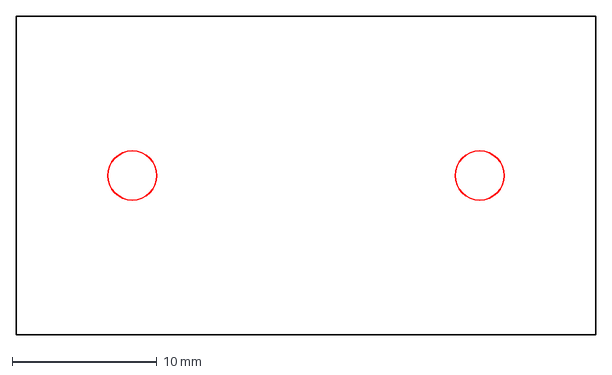
[picture p123: CAD file, 2026-10-08]
panel/dashboard/cnc/splice_small.dxf
40.0 x 22.0 mm
