SFXShannon/c172-home-sim/panel/dashboard/stl/tile_M2.stl

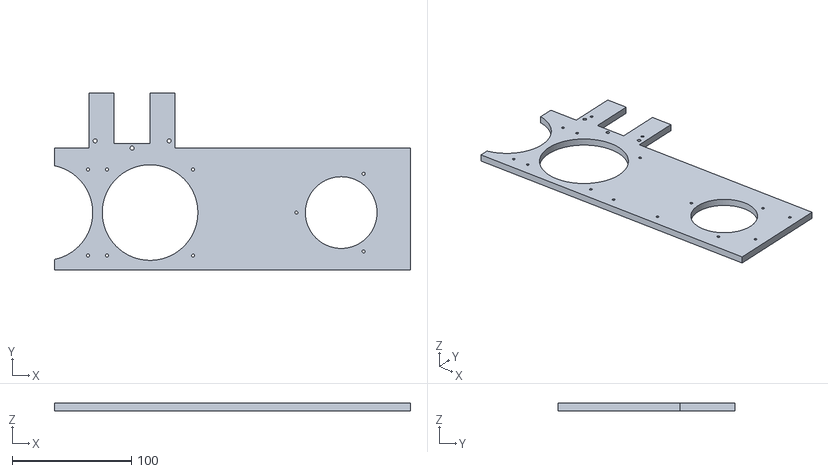
[picture p124: CAD file, 2026-10-08]
panel/dashboard/stl/tile_M2.stl
298.0 x 148.0 x 6.35
