SFXShannon/c172-home-sim/parts/fuel-selector/stl/handle_gear.stl

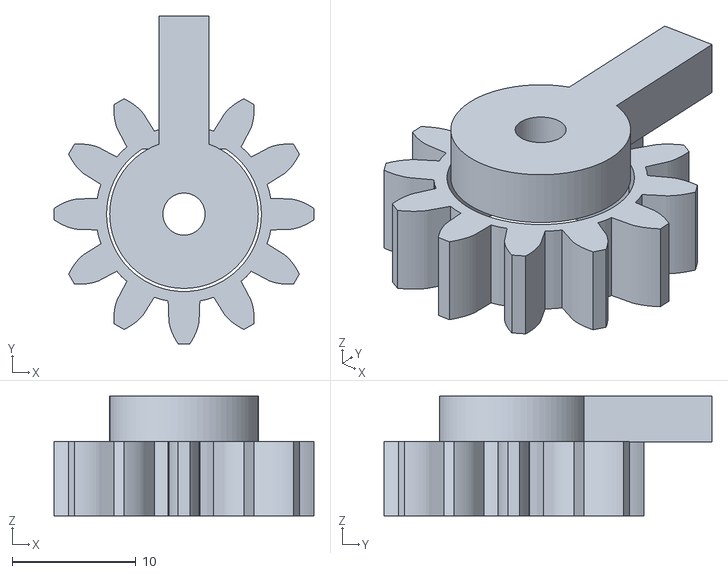
[picture p125: CAD file, 2026-10-08]
parts/fuel-selector/stl/handle_gear.stl
21.0 x 26.5 x 9.69
