SFXShannon/c172-home-sim/parts/g1000-gdu/stl/switch_plate_right.stl

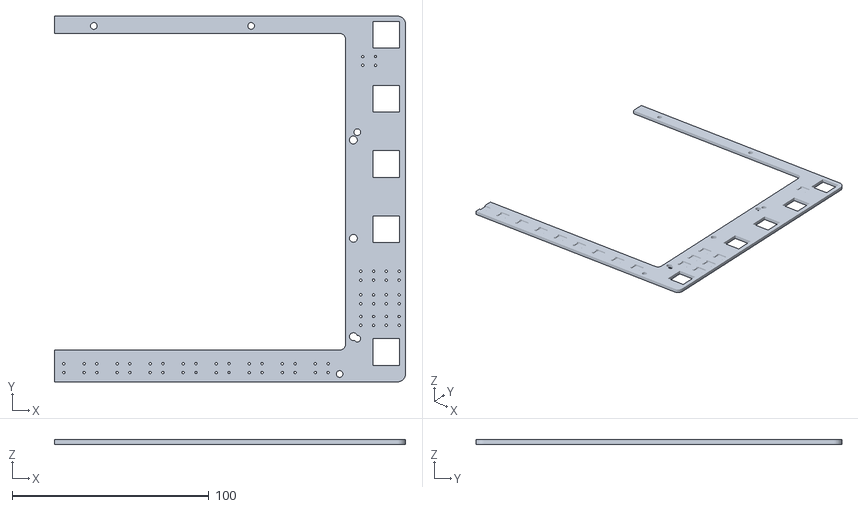
[picture p126: CAD file, 2026-10-08]
parts/g1000-gdu/stl/switch_plate_right.stl
178.5 x 186.0 x 2.50
