SFXShannon/c172-home-sim/parts/panel-extras/stl/knob_cabin_air.stl

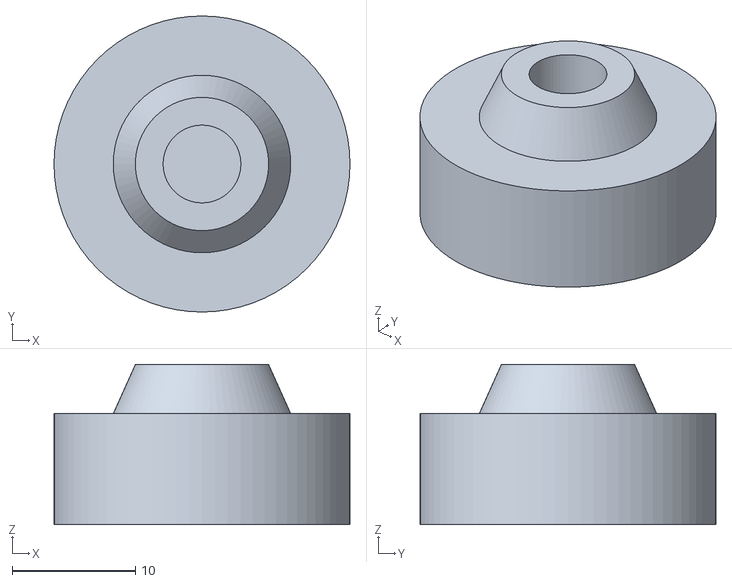
[picture p127: CAD file, 2026-10-08]
parts/panel-extras/stl/knob_cabin_air.stl
24.0 x 24.0 x 13.0
