SFXShannon/c172-home-sim/panel/dashboard/cnc/pedestal_floor.dxf

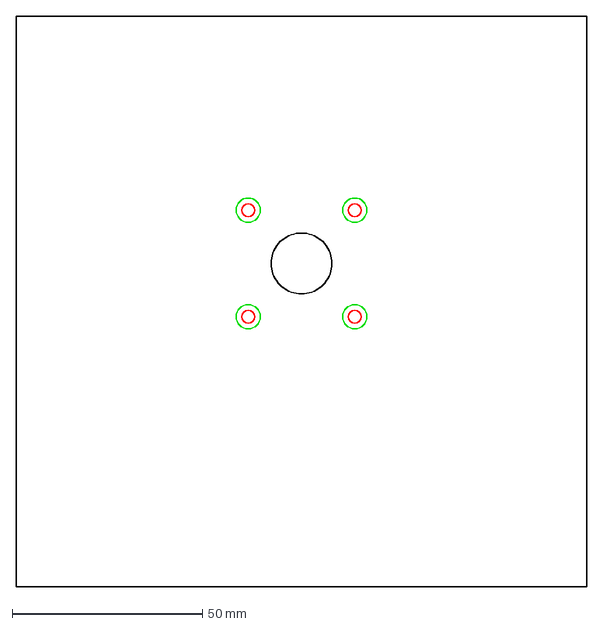
[picture p128: CAD file, 2026-10-08]
panel/dashboard/cnc/pedestal_floor.dxf
150.0 x 150.0 mm
