SFXShannon/c172-home-sim/panel/dashboard/stl/tile_L3.stl

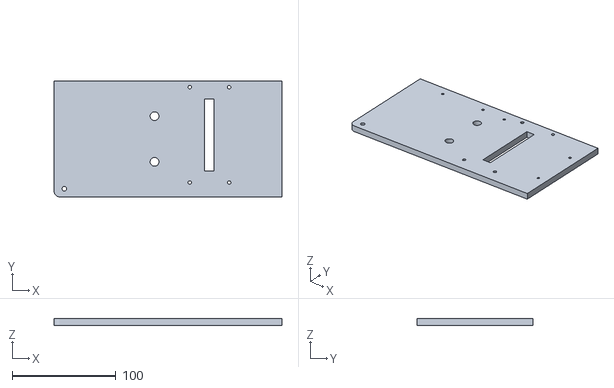
[picture p129: CAD file, 2026-10-08]
panel/dashboard/stl/tile_L3.stl
220.0 x 112.0 x 6.35
