SFXShannon/c172-home-sim/parts/fuel-selector/stl/panel_test_plate.stl

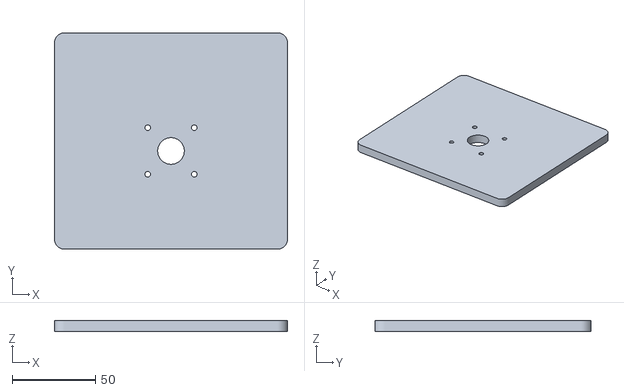
[picture p130: CAD file, 2026-10-08]
parts/fuel-selector/stl/panel_test_plate.stl
140.0 x 130.0 x 6.35
