SFXShannon/c172-home-sim/parts/g1000-gdu/stl/lcd_cradle_left.stl

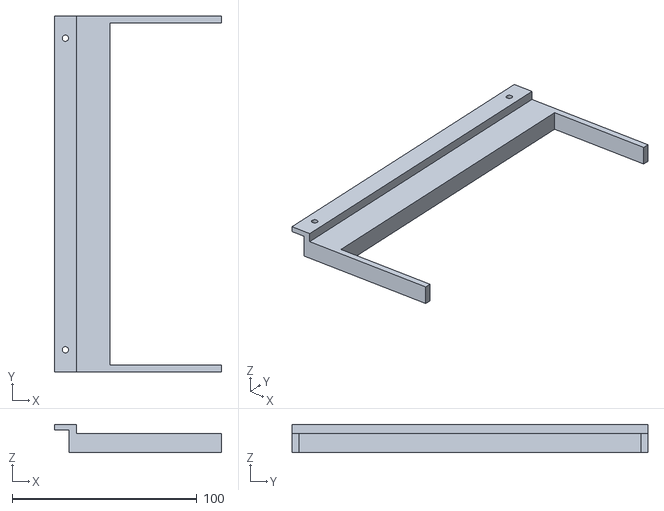
[picture p131: CAD file, 2026-10-08]
parts/g1000-gdu/stl/lcd_cradle_left.stl
90.5 x 192.5 x 15.1
