SFXShannon/c172-home-sim/parts/panel-extras/stl/ignition_key.stl

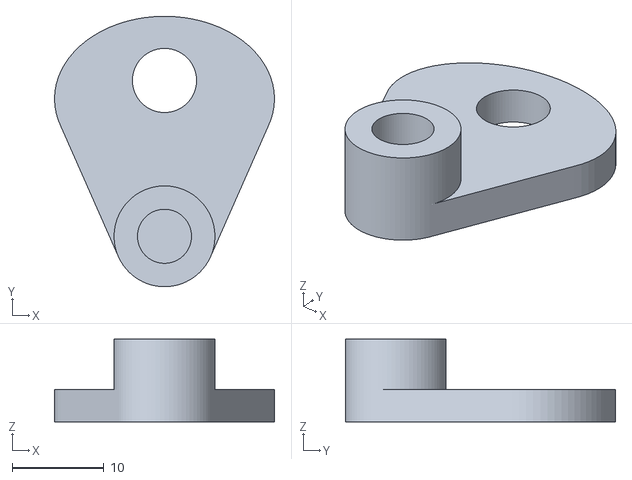
[picture p132: CAD file, 2026-10-08]
parts/panel-extras/stl/ignition_key.stl
24.0 x 29.5 x 9.00
