SFXShannon/c172-home-sim/panel/dashboard/cnc/upper_1.dxf

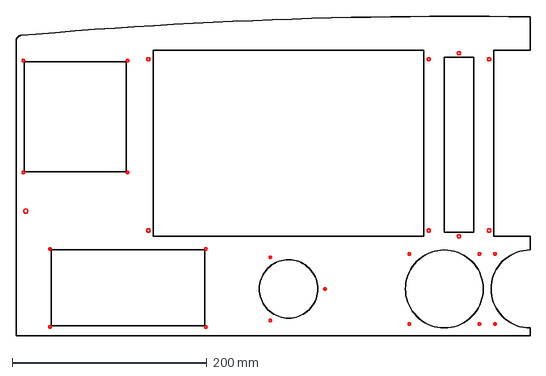
[picture p133: CAD file, 2026-10-08]
panel/dashboard/cnc/upper_1.dxf
528.0 x 328.0 mm
