SFXShannon/c172-home-sim/panel/dashboard/stl/glareshield_2.stl

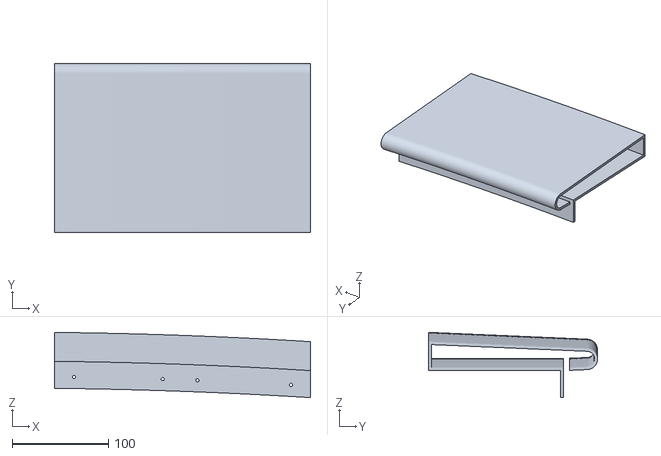
[picture p134: CAD file, 2026-10-08]
panel/dashboard/stl/glareshield_2.stl
265.5 x 175.3 x 67.6
