SFXShannon/c172-home-sim/parts/fuel-selector/stl/handle.stl

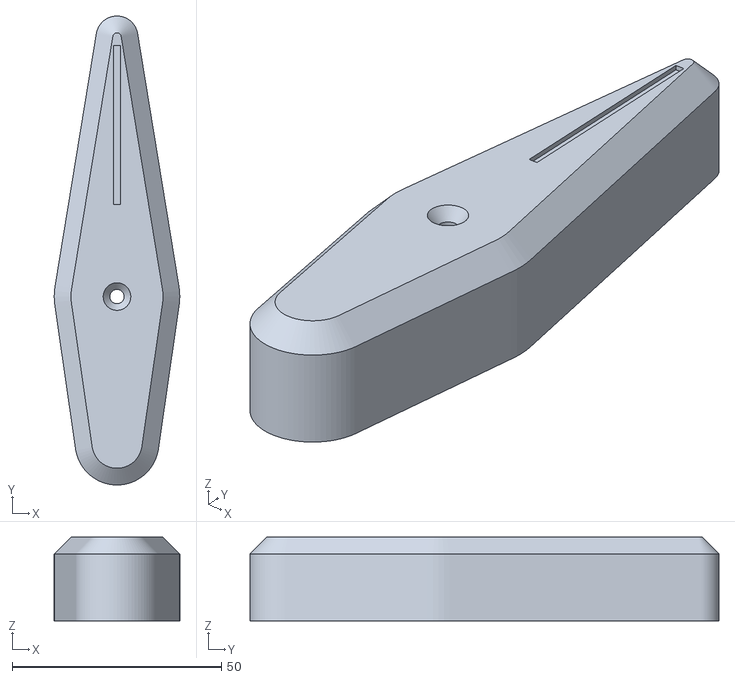
[picture p135: CAD file, 2026-10-08]
parts/fuel-selector/stl/handle.stl
30.0 x 112.0 x 20.0
