SFXShannon/c172-home-sim/parts/panel-extras/stl/knob_fuel_shutoff.stl

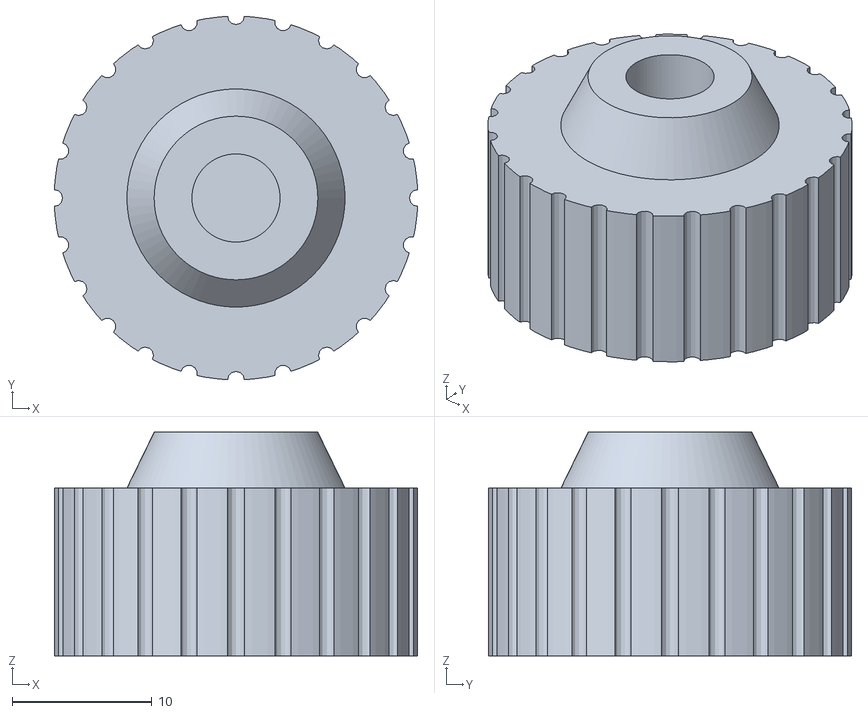
[picture p136: CAD file, 2026-10-08]
parts/panel-extras/stl/knob_fuel_shutoff.stl
25.9 x 25.9 x 16.0
