SFXShannon/c172-home-sim/panel/dashboard/cnc/upper_2.dxf

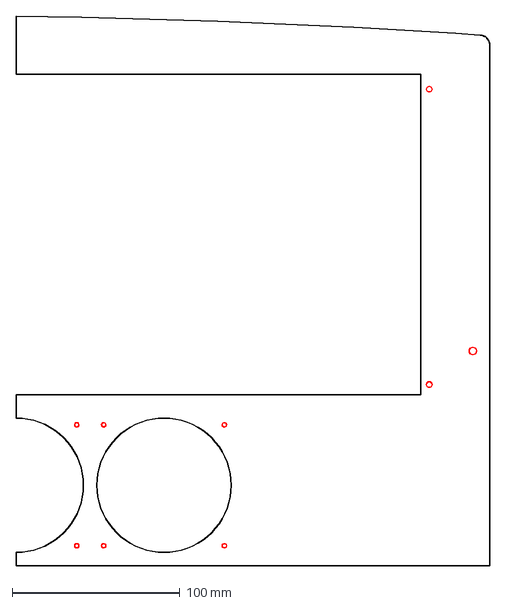
[picture p137: CAD file, 2026-10-08]
panel/dashboard/cnc/upper_2.dxf
282.0 x 327.5 mm
