SFXShannon/c172-home-sim/panel/dashboard/stl/tile_U2.stl

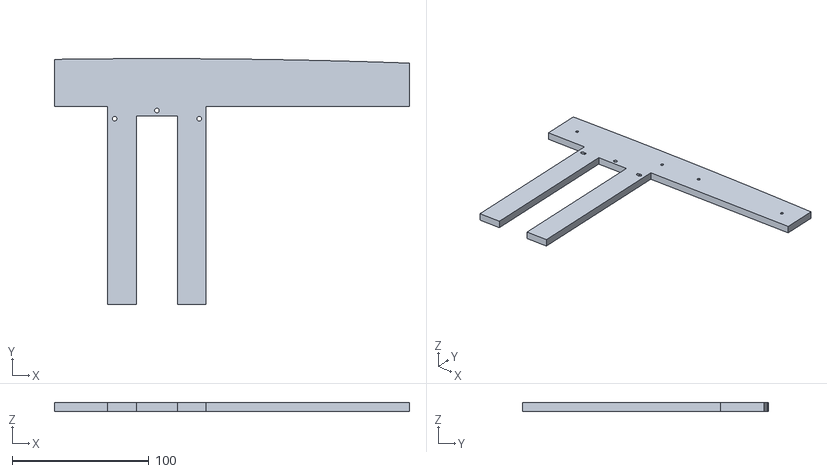
[picture p138: CAD file, 2026-10-08]
panel/dashboard/stl/tile_U2.stl
260.0 x 180.0 x 6.35
