SFXShannon/c172-home-sim/parts/g1000-gdu/stl/knobs_sheet.stl

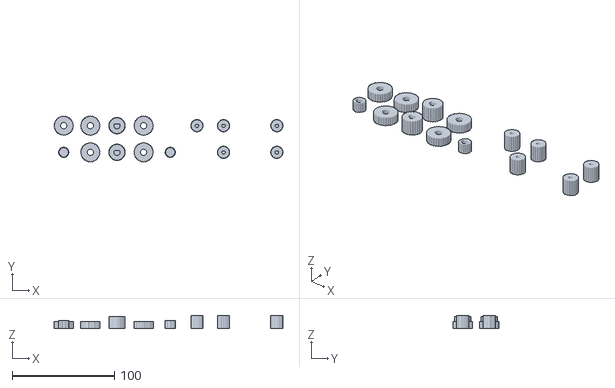
[picture p139: CAD file, 2026-10-08]
parts/g1000-gdu/stl/knobs_sheet.stl
223.5 x 45.0 x 13.0
