SFXShannon/c172-home-sim/parts/panel-extras/stl/ignition_escutcheon.stl

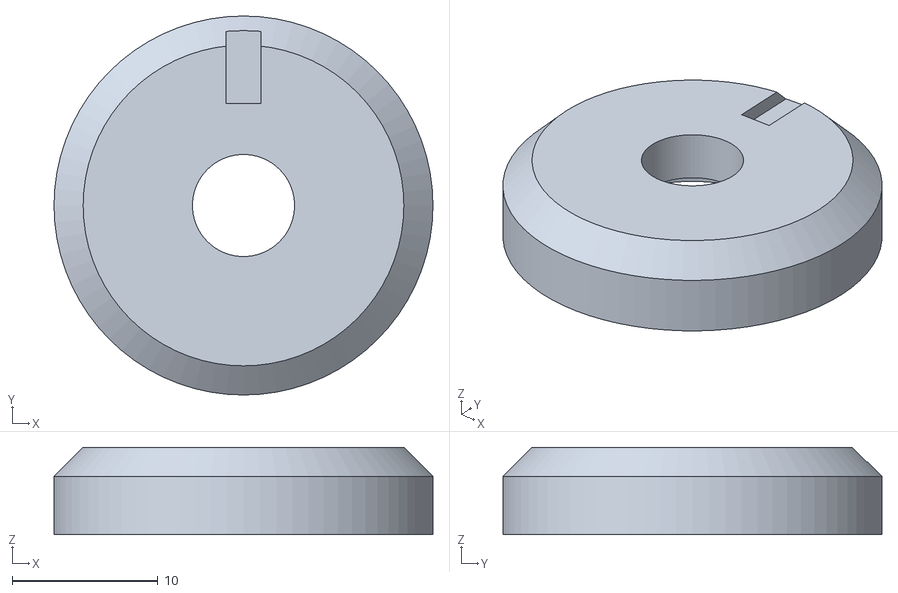
[picture p140: CAD file, 2026-10-08]
parts/panel-extras/stl/ignition_escutcheon.stl
26.0 x 26.0 x 6.00
