SFXShannon/c172-home-sim/parts/g1000-gdu/stl/switch_plate_left.stl

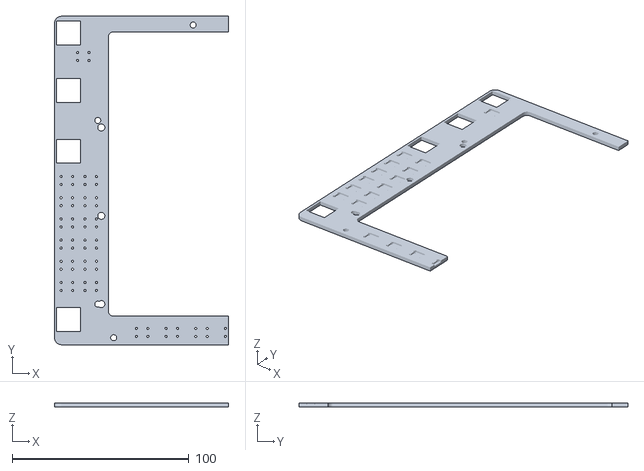
[picture p142: CAD file, 2026-10-08]
parts/g1000-gdu/stl/switch_plate_left.stl
98.5 x 186.0 x 2.50
