SFXShannon/c172-home-sim/panel/dashboard/stl/tile_M3.stl

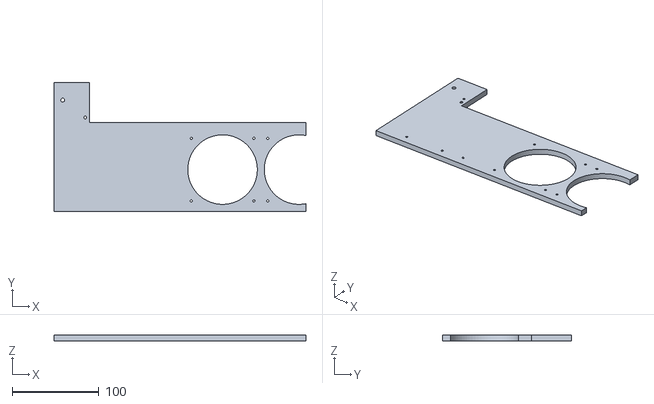
[picture p144: CAD file, 2026-10-08]
panel/dashboard/stl/tile_M3.stl
290.0 x 148.0 x 6.35
