SFXShannon/c172-home-sim/panel/dashboard/cnc/splice.dxf

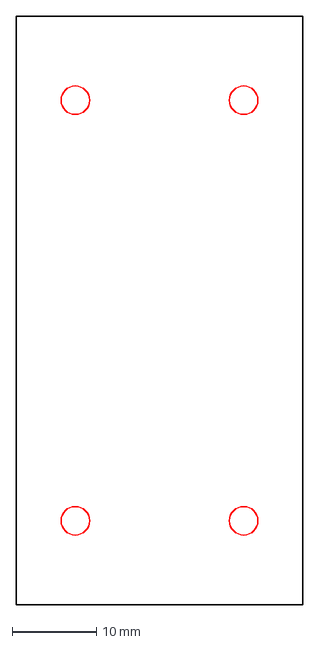
[picture p145: CAD file, 2026-10-08]
panel/dashboard/cnc/splice.dxf
34.0 x 70.0 mm
