SFXShannon/c172-home-sim/panel/dashboard/stl/tile_U1.stl

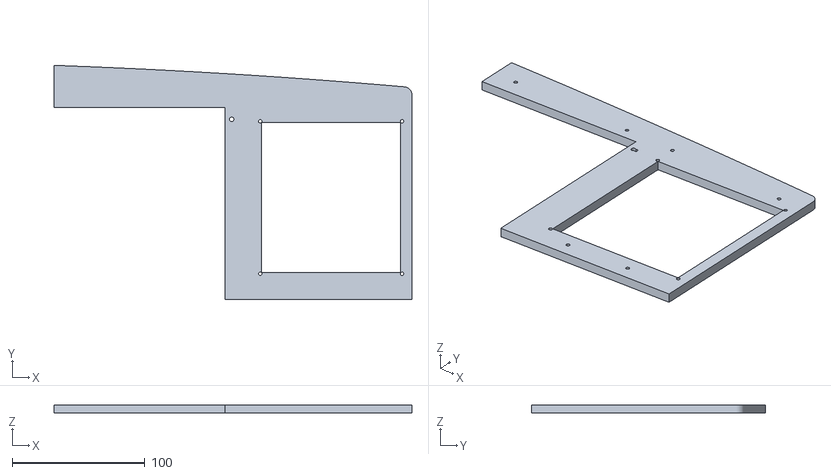
[picture p146: CAD file, 2026-10-08]
panel/dashboard/stl/tile_U1.stl
270.0 x 176.7 x 6.35
