SFXShannon/c172-home-sim/panel/dashboard/stl/splice_small.stl

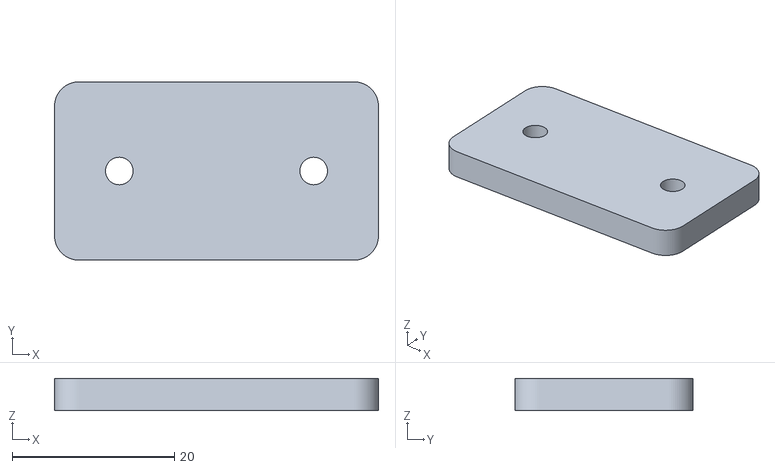
[picture p147: CAD file, 2026-10-08]
panel/dashboard/stl/splice_small.stl
40.0 x 22.0 x 4.00
