SFXShannon/c172-home-sim/panel/dashboard/stl/tile_M1.stl

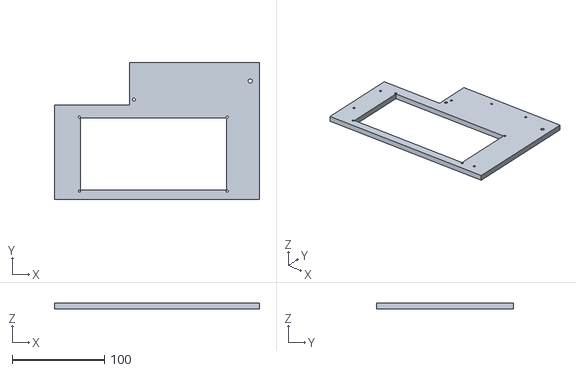
[picture p148: CAD file, 2026-10-08]
panel/dashboard/stl/tile_M1.stl
222.0 x 148.0 x 6.35
