SFXShannon/c172-home-sim/panel/dashboard/stl/glareshield_4.stl

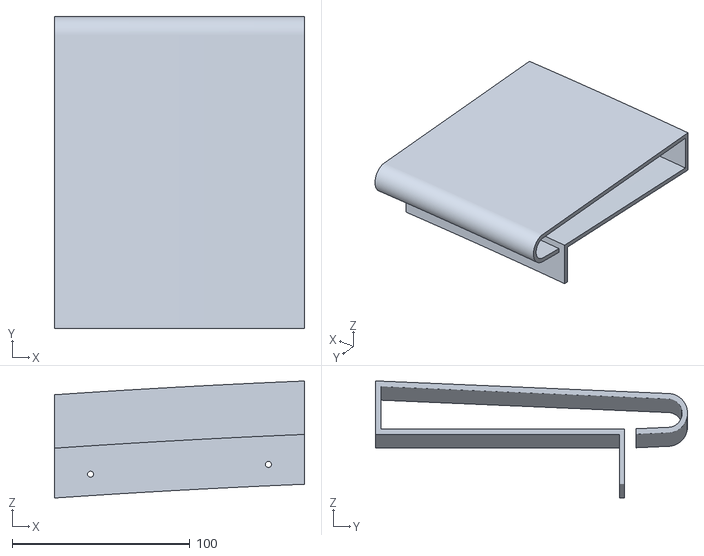
[picture p149: CAD file, 2026-10-08]
panel/dashboard/stl/glareshield_4.stl
140.5 x 175.3 x 65.7
