SFXShannon/c172-home-sim/panel/splices.scad

// Written by scripts/place_splices.py - re-run it after moving things or changing the seams.
splices = [[15, 55.5, "V"], [310, 55.5, "V"], [-58, 169.5, "V"], [-260.5, 112, "h"], [71.5, 112, "H"], [416.5, 112, "h"], [469.5, 112, "H"], [-212.5, 260, "H"]];
cnc_splices = [[15, 55.5, "V"], [-260.5, 112, "h"], [-69.5, 112, "h"], [71.5, 112, "H"], [416.5, 112, "h"], [469.5, 112, "H"]];
